SauceSpoon/RBE206TC-submission/ESP32-source/camera璇嗗埆妯″瀷/瑙嗚绯荤粺鏂规.md

颜色分割定位候选区域
CNN 确认形状
摄像头上下扫视扩大视野
连续多帧投票降低误判
机器人慢速接近并持续复核
