SauceSpoon/RBE206TC-submission/ESP32-source/competition plan.pdf

# Competition

RBE206TC

1.5 m

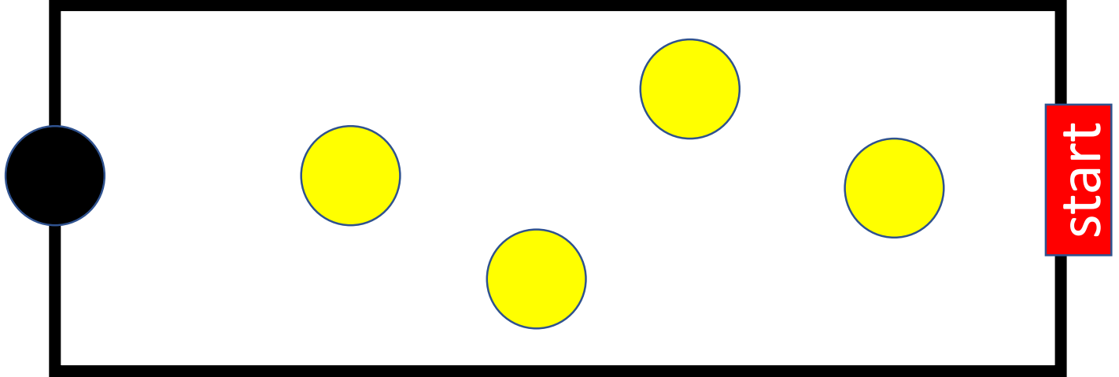
[picture p53: figure]
start

0.6 m

## Task 1

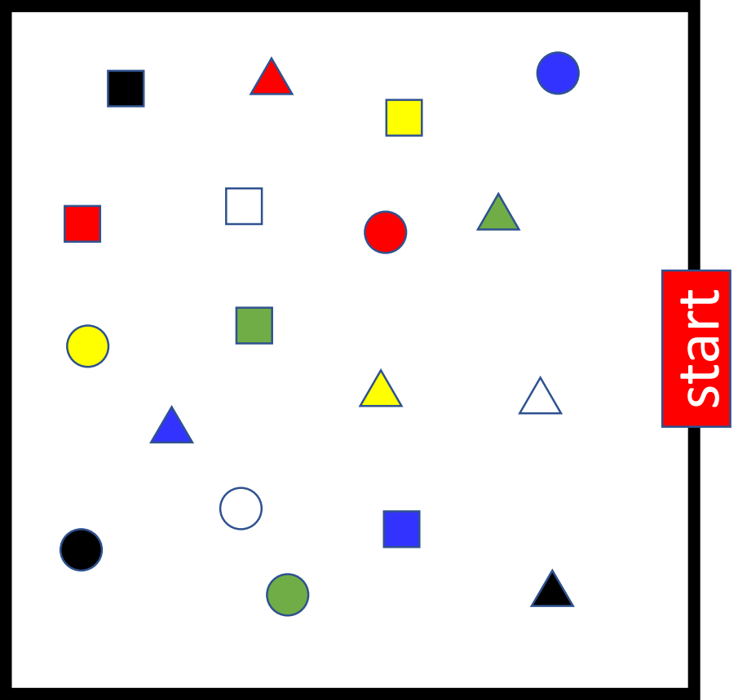
[picture p54: figure]
start

1 m

## Task 2

## Task process

- Phase 1
- Reach the goal
- Touch the black column
- Obstacle avoidance
- 4 obstacles (yellow column)
- Time elapse
- Phase 2
- Select a color and a shape
- Random selection
- Touch the specific object (color and shape)

## - 2 trials - Pick a better performance - Complete a phase before starting the next phase
