SauceSpoon/RBE206TC-submission/oodk(CAD model)/odk4（Generation 4）/cam_mera.SLDASM

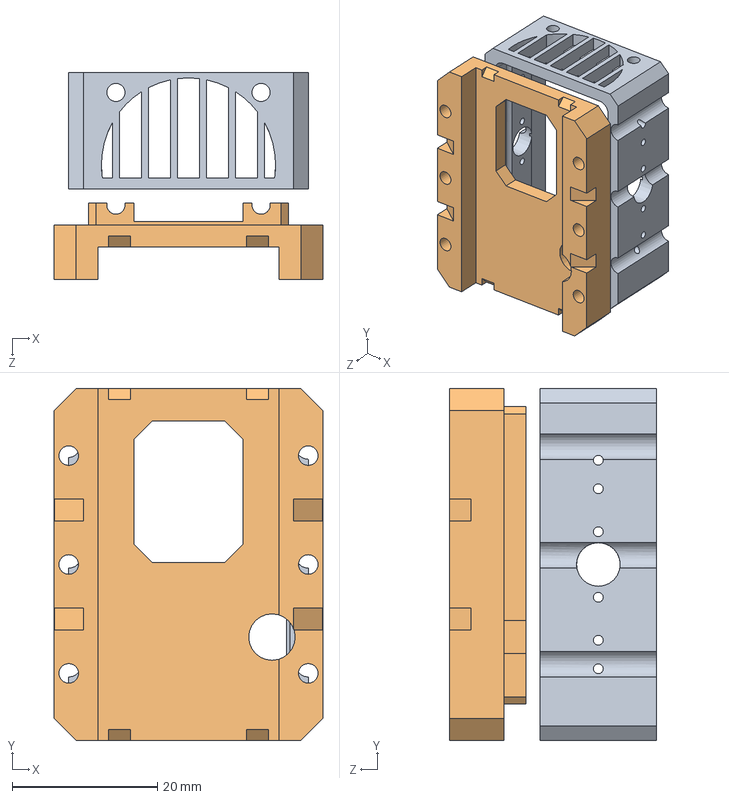
[picture p65: CAD file, 2026-05-20]
oodk(CAD model)/odk4（Generation 4）/cam_mera.SLDASM
37.0 x 48.5 x 28.5 mm
摄像机壳1
摄像机壳2
