SauceSpoon/RBE206TC-submission/oodk(CAD model)/odk2（Generation 2）/odk3.SLDASM

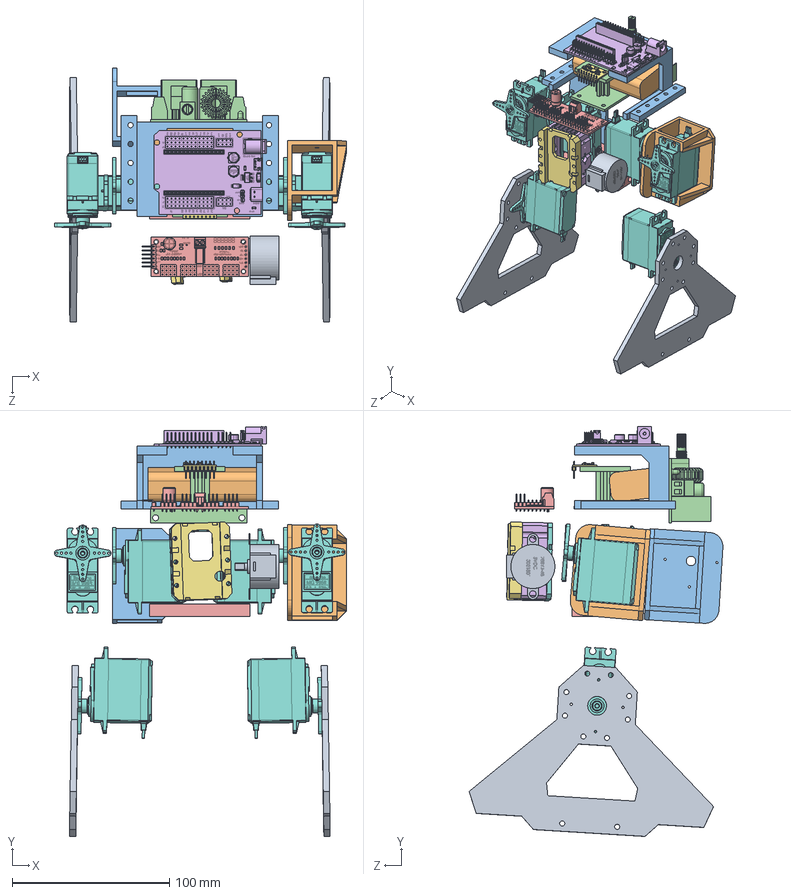
[picture p66: CAD file, 2026-05-20]
oodk(CAD model)/odk2（Generation 2）/odk3.SLDASM
185.7 x 260.6 x 161.3 mm
十字舵机 x 6
MPU6050
ESP32拓展板26
PCA9685
XH-M401 Buck converter (XL4016E1)
esp32_dc
LB218B
Step Motor 28BYJ-48
摄像机壳3
摄像机壳1
摄像机壳2
横_
MPU
髋部连接件-右
髋部连接件-左
