SauceSpoon/RBE206TC-submission/oodk(CAD model)/odk2（Generation 2）/髋.SLDASM

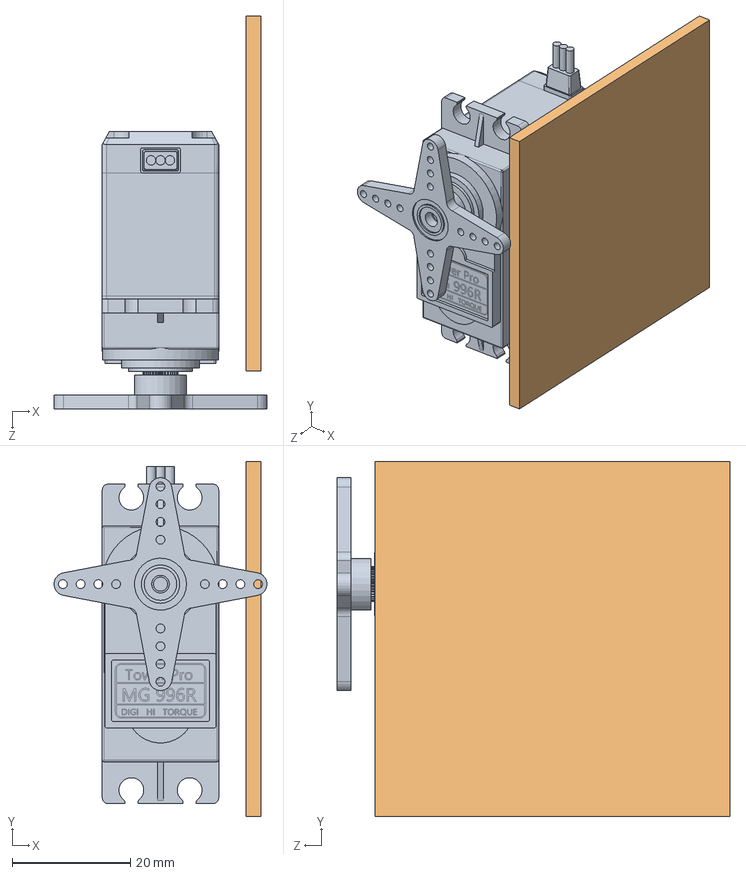
[picture p67: CAD file, 2026-05-20]
oodk(CAD model)/odk2（Generation 2）/髋.SLDASM
36.0 x 60.0 x 66.4 mm
髋连接件
十字舵机
