SauceSpoon/RBE206TC-submission/oodk(CAD model)/odk4（Generation 4）/PCA9685.SLDPRT

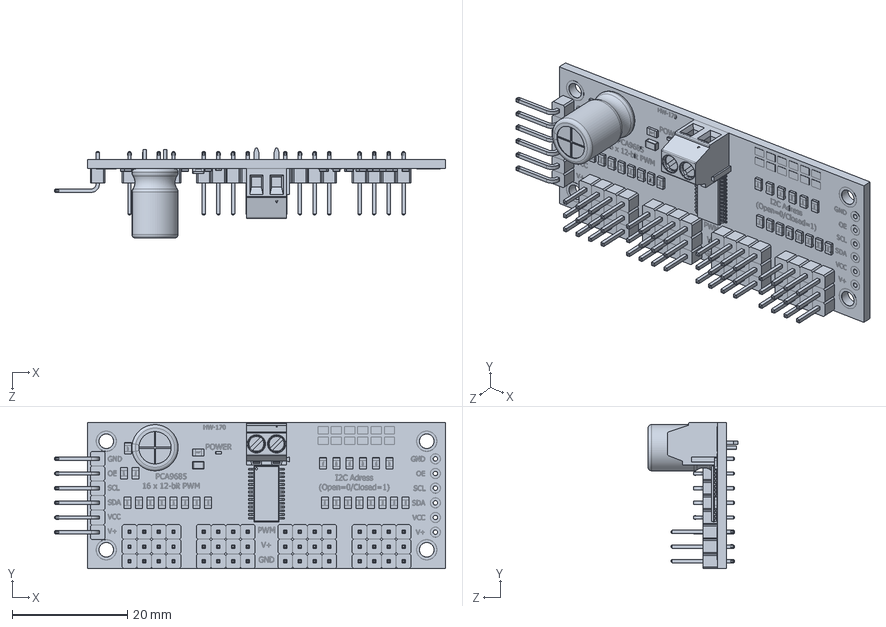
[picture p73: CAD file, 2026-05-20]
oodk(CAD model)/odk4（Generation 4）/PCA9685.SLDPRT
67.7 x 25.3 x 15.6 mm
