SauceSpoon/RBE206TC-submission/oodk(CAD model)/odk4（Generation 4）/print/ESP32-cam.step

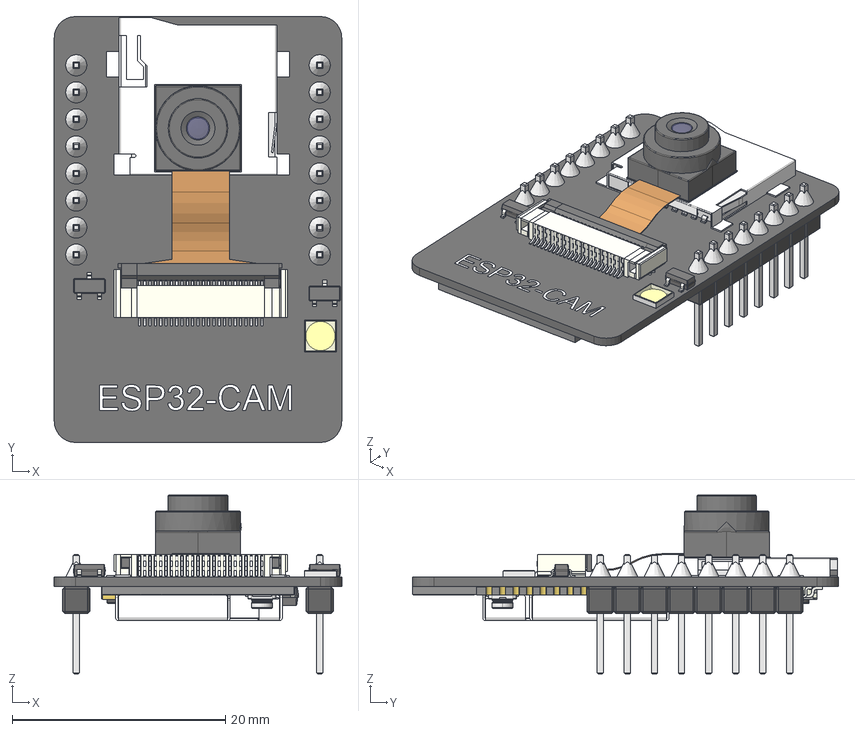
[picture p74: CAD file, 2026-05-20]
oodk(CAD model)/odk4（Generation 4）/print/ESP32-cam.step
27.0 x 40.0 x 16.8 mm
PCB
WiFi antenna
uid__2363^DesignRootModel_PCB_ESP32-S2-SOLO-U_V1_ESP32-S2-SOLO-U_V1
uid__1-263^DesignRootModel_PCB_ESP32-S2-SOLO-U_V1_ESP32-S2-SOLO-U_V1
uid__1-264^DesignRootModel_PCB_ESP32-S2-SOLO-U_V1_ESP32-S2-SOLO-U_V1
20279-001E-01C RECEPTACLE R9 STEP ALL.STEP^20279-001E-01C RECEPTACLE R9 STEP ALL.STEP_Submodel-IPEX_3P_part_DesignRootModel_PCB_ESP32-S2-SOLO-U_V1_ ESP32-S2-SOL
20279-001E-01C RECEPTACLE R9 STEP ALL.STEP^20279-001E-01C RECEPTACLE R9 STEP ALL.STEP_Submodel-IPEX_3P_part_DesignRootModel_PCB_ESP32-S2-SOLO-U_V1_ ESP32-S2-SOL
ESP32-WROOM-32U_Shieldingcase_20210312
SOIC_8_1EP_39x49mm_P127mm
SW_SPST_B3U-1000P
SOT_223
CP_EIA_3528_12_Kemet_T
FPC-24
FPC-025
FPC-026
FPC-027
FPC-028
FPC-029
FPC-030
FPC-031
FPC-032
FPC-033
FPC-034
FPC-035
FPC-036
FPC-037
FPC-038
FPC-039
FPC-040
scotxh
SOT_23-1
SOT_23-2
Text
