SauceSpoon/RBE206TC-submission/oodk(CAD model)/odk2（Generation 2）/28BYJ-48步进电机和ULN2003步进电机驱动板/28BYJ-48_5VDC.step

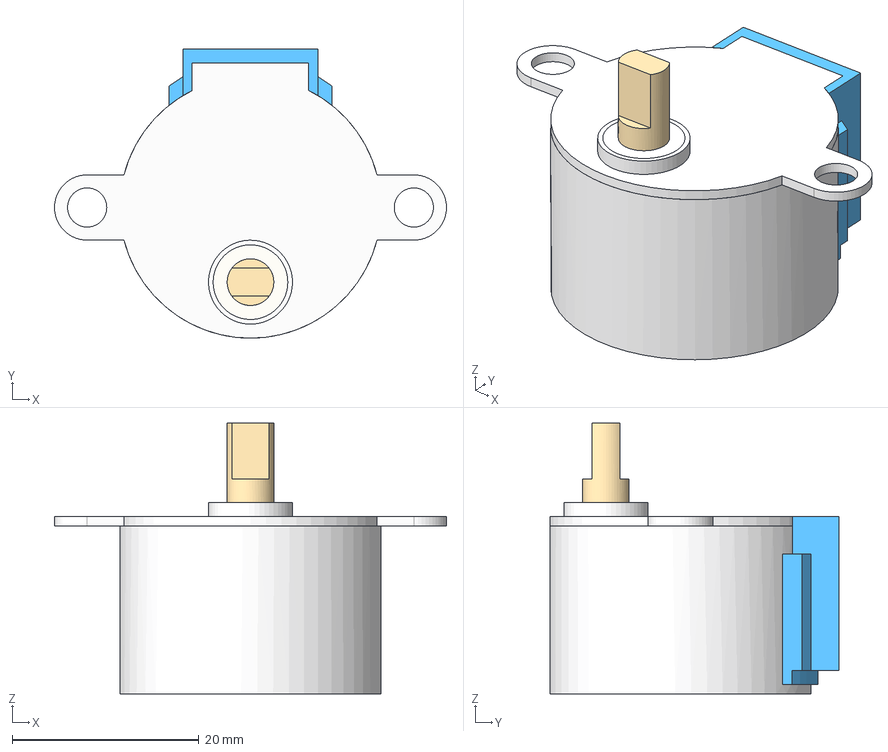
[picture p76: CAD file, 2026-05-20]
oodk(CAD model)/odk2（Generation 2）/28BYJ-48步进电机和ULN2003步进电机驱动板/28BYJ-48_5VDC.step
42.0 x 31.0 x 29.0 mm
