SauceSpoon/RBE206TC-submission/oodk(CAD model)/odk2（Generation 2）/髋连接件.SLDPRT

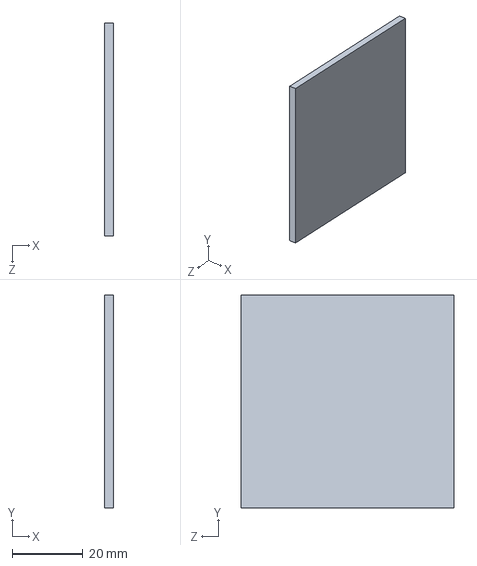
[picture p77: CAD file, 2026-05-20]
oodk(CAD model)/odk2（Generation 2）/髋连接件.SLDPRT
2.50 x 60.0 x 60.0 mm
