SauceSpoon/RBE206TC-submission/oodk(CAD model)/odk3（Generation 3）/print/22.STEP

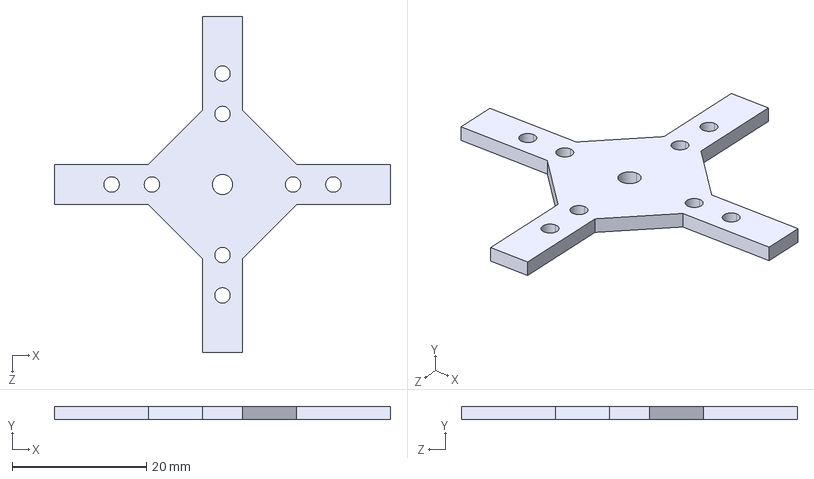
[picture p78: CAD file, 2026-05-20]
oodk(CAD model)/odk3（Generation 3）/print/22.STEP
50.0 x 2.00 x 50.0 mm
