SauceSpoon/RBE206TC-submission/oodk(CAD model)/odk3（Generation 3）/横_.SLDPRT

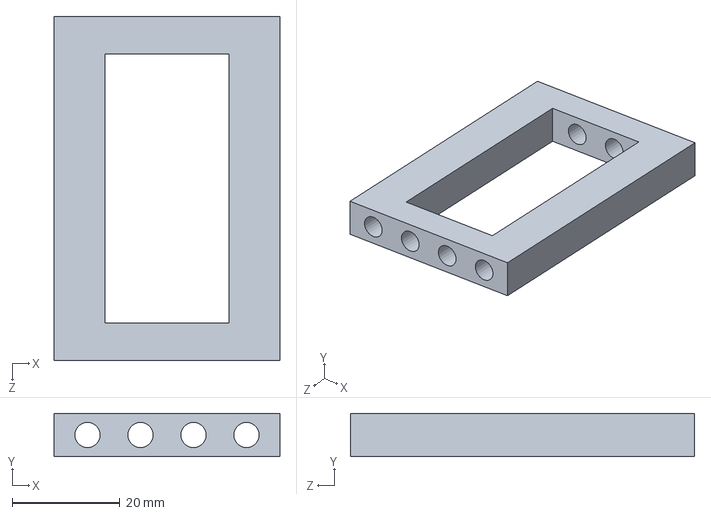
[picture p79: CAD file, 2026-05-20]
oodk(CAD model)/odk3（Generation 3）/横_.SLDPRT
42.0 x 8.00 x 64.0 mm
