SauceSpoon/RBE206TC-submission/oodk(CAD model)/odk4（Generation 4）/camera_g.SLDPRT

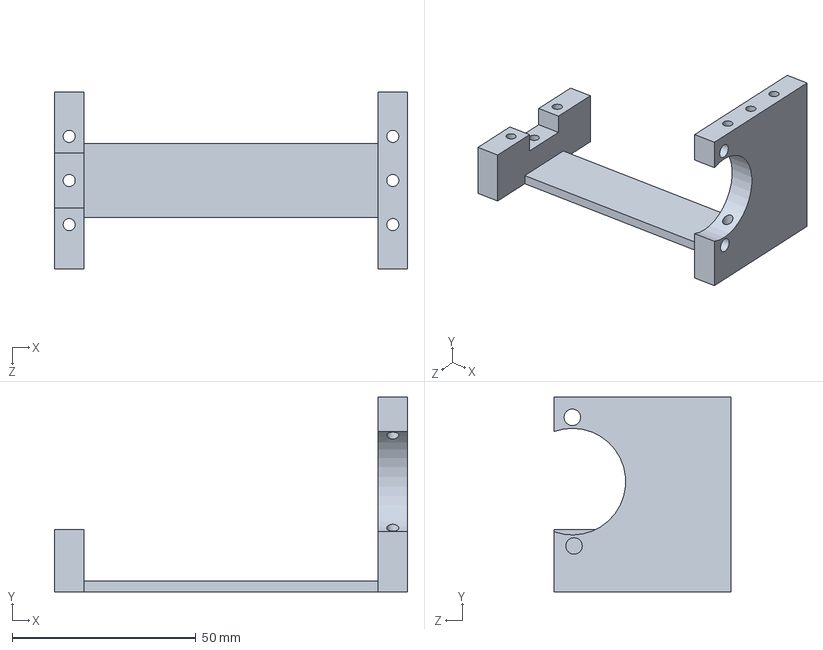
[picture p80: CAD file, 2026-05-20]
oodk(CAD model)/odk4（Generation 4）/camera_g.SLDPRT
96.0 x 53.0 x 48.1 mm
