SauceSpoon/RBE206TC-submission/oodk(CAD model)/odk4（Generation 4）/print/新plat.STEP

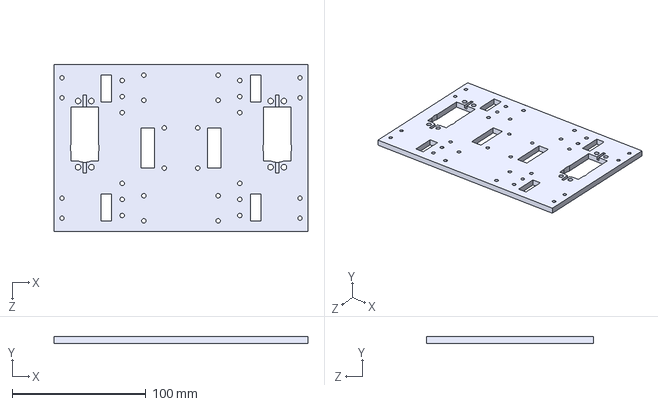
[picture p81: CAD file, 2026-05-20]
oodk(CAD model)/odk4（Generation 4）/print/新plat.STEP
190.0 x 5.00 x 125.0 mm
