SauceSpoon/RBE206TC-submission/oodk(CAD model)/odk1（Generation 1）/髋部连接件-左.SLDPRT

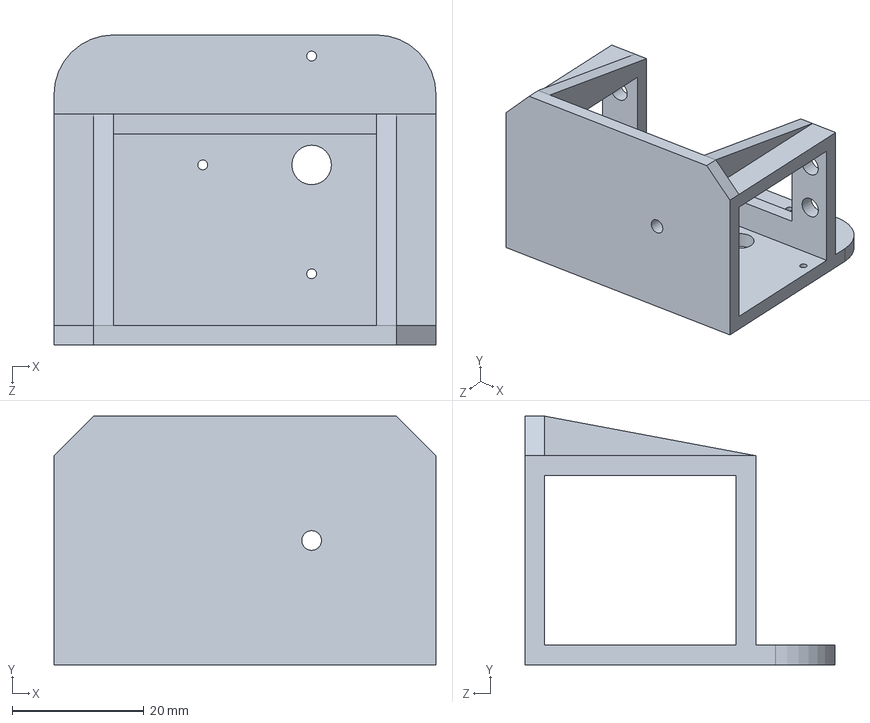
[picture p82: CAD file, 2026-05-20]
oodk(CAD model)/odk1（Generation 1）/髋部连接件-左.SLDPRT
57.9 x 37.7 x 47.0 mm
