SauceSpoon/RBE206TC-submission/oodk(CAD model)/odk2（Generation 2）/332.SLDPRT

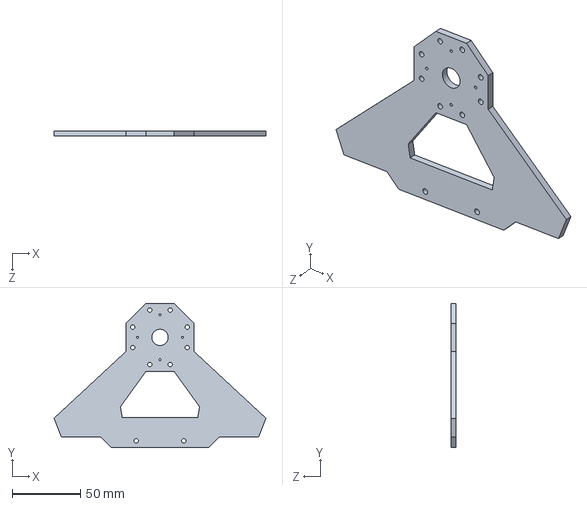
[picture p83: CAD file, 2026-05-20]
oodk(CAD model)/odk2（Generation 2）/332.SLDPRT
155.7 x 106.0 x 4.00 mm
