SauceSpoon/RBE206TC-submission/oodk(CAD model)/odk3（Generation 3）/print/板1.STEP

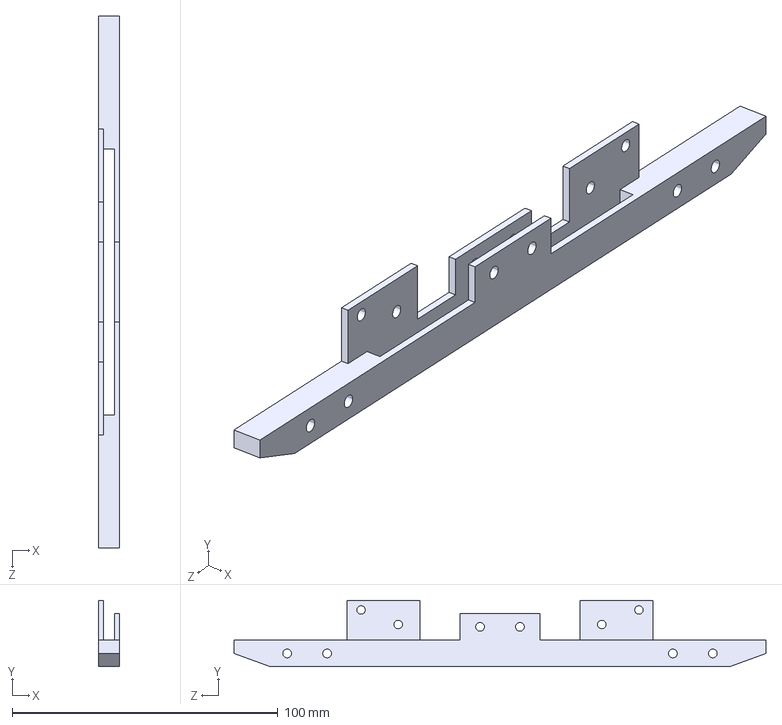
[picture p84: CAD file, 2026-05-20]
oodk(CAD model)/odk3（Generation 3）/print/板1.STEP
8.00 x 25.0 x 200.0 mm
