SauceSpoon/RBE206TC-submission/oodk(CAD model)/odk3（Generation 3）/摄像机壳1.SLDPRT

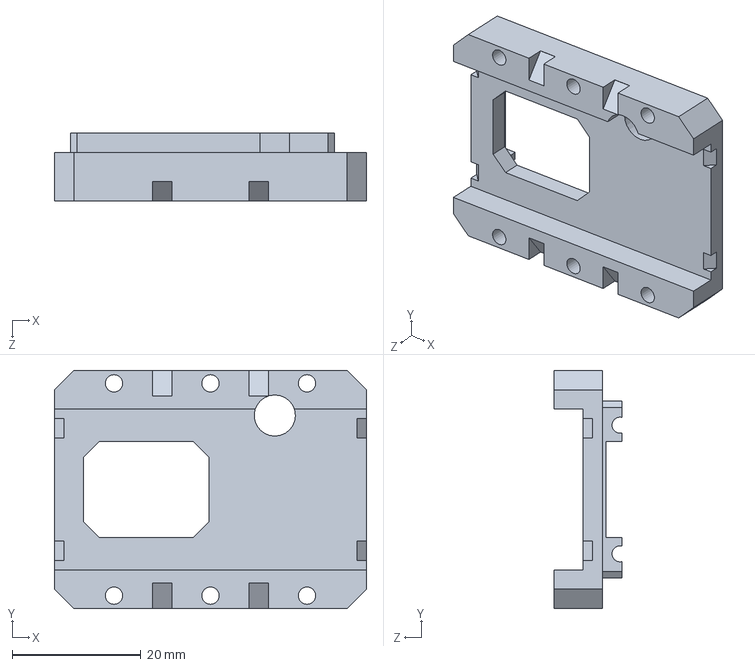
[picture p85: CAD file, 2026-05-20]
oodk(CAD model)/odk3（Generation 3）/摄像机壳1.SLDPRT
48.5 x 37.0 x 10.5 mm
