SauceSpoon/RBE206TC-submission/oodk(CAD model)/odk4（Generation 4）/MPU6050.SLDPRT

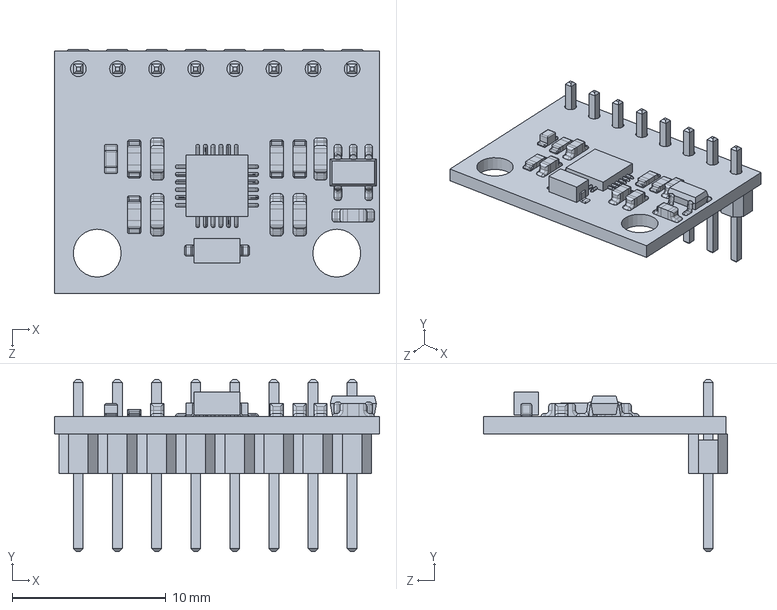
[picture p86: CAD file, 2026-05-20]
oodk(CAD model)/odk4（Generation 4）/MPU6050.SLDPRT
21.1 x 11.2 x 15.9 mm
