SauceSpoon/RBE206TC-submission/oodk(CAD model)/odk1（Generation 1）/小腿.SLDPRT

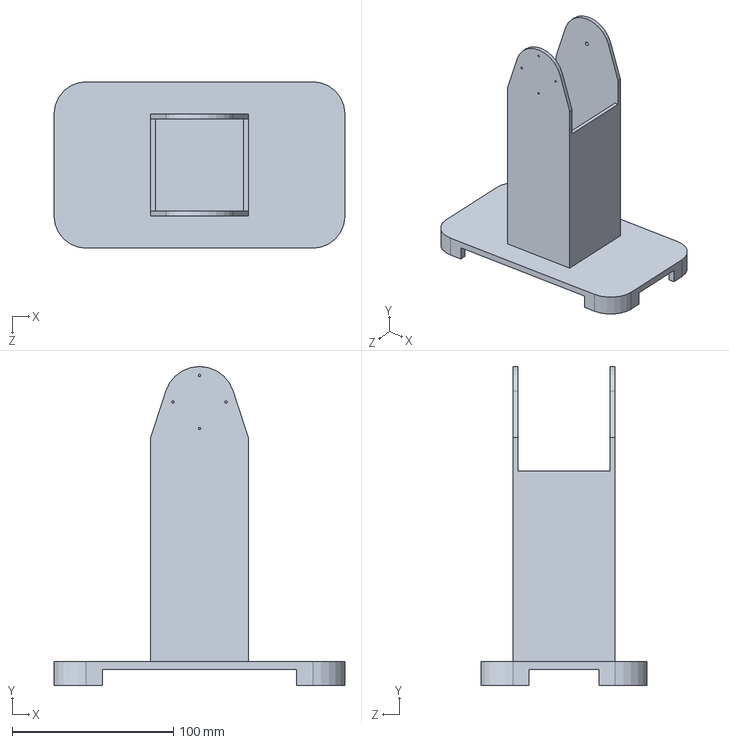
[picture p87: CAD file, 2026-05-20]
oodk(CAD model)/odk1（Generation 1）/小腿.SLDPRT
180.6 x 198.0 x 103.3 mm
