SauceSpoon/RBE206TC-submission/oodk(CAD model)/odk2（Generation 2）/print/架.STEP

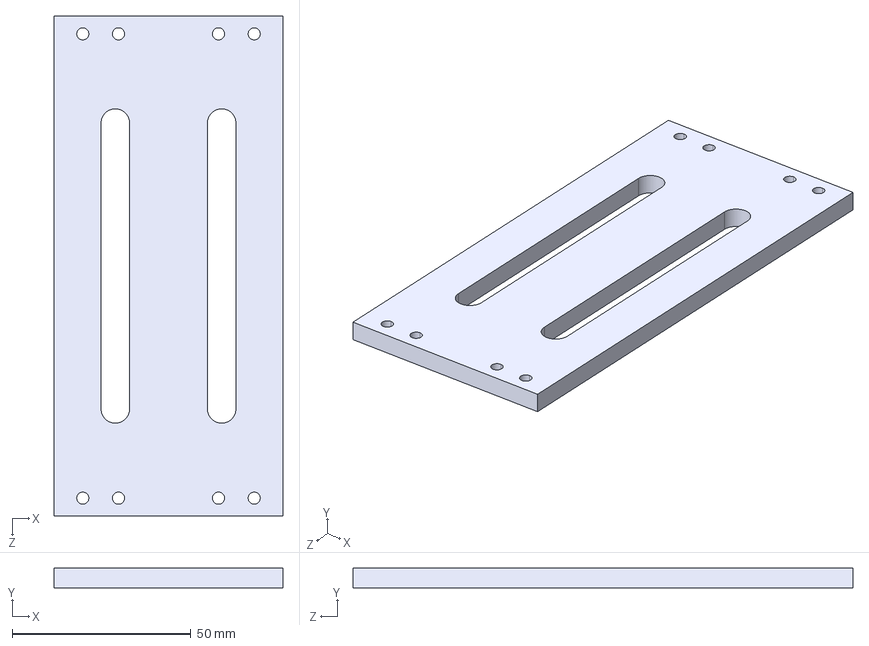
[picture p88: CAD file, 2026-05-20]
oodk(CAD model)/odk2（Generation 2）/print/架.STEP
64.0 x 5.50 x 140.0 mm
