SauceSpoon/RBE206TC-submission/oodk(CAD model)/odk4（Generation 4）/MPU.SLDPRT

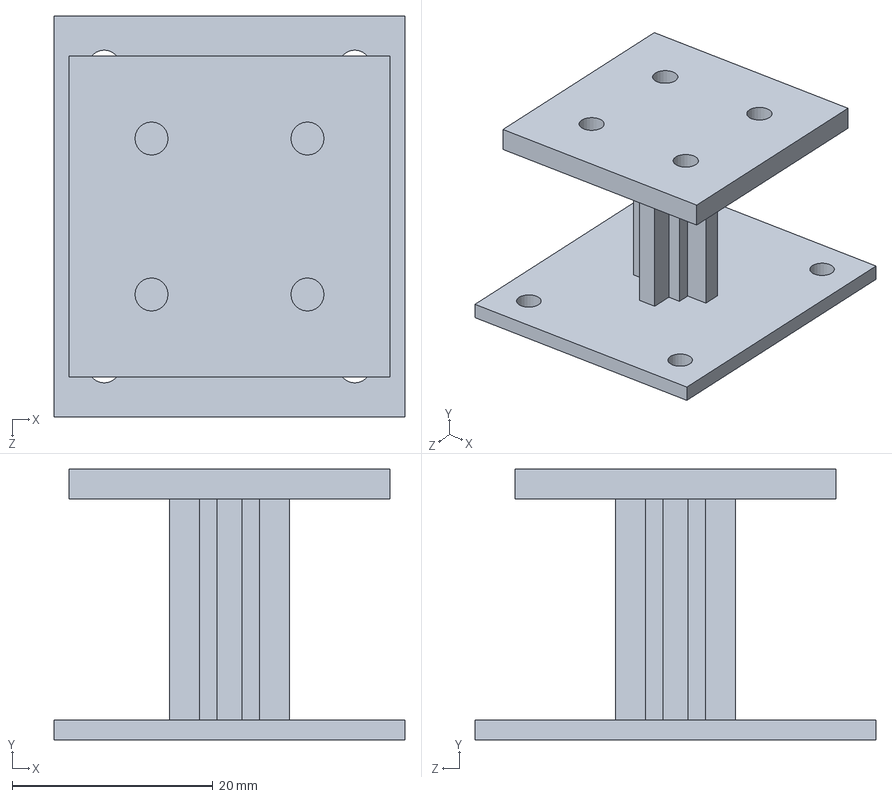
[picture p89: CAD file, 2026-05-20]
oodk(CAD model)/odk4（Generation 4）/MPU.SLDPRT
35.0 x 27.0 x 40.0 mm
