SauceSpoon/RBE206TC-submission/oodk(CAD model)/odk2（Generation 2）/print/Mirrorthigh2.3mf

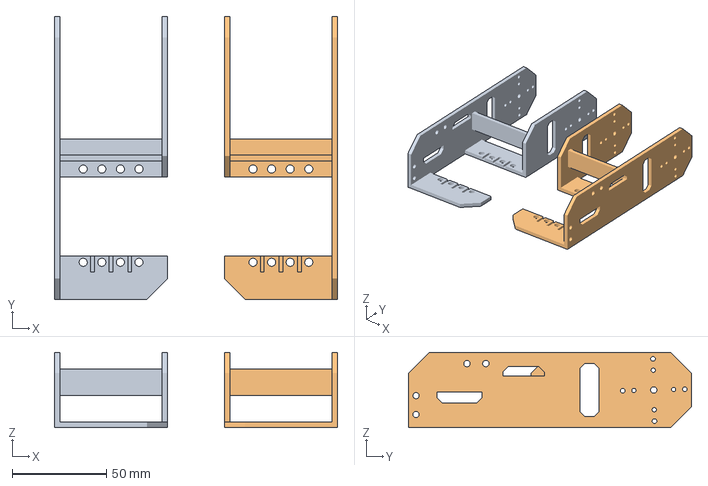
[picture p91: CAD file, 2026-05-20]
oodk(CAD model)/odk2（Generation 2）/print/Mirrorthigh2.3mf
150.0 x 150.0 x 40.0 mm
thigh.STEP
Mirrorthigh.STEP
