SauceSpoon/RBE206TC-submission/oodk(CAD model)/odk2（Generation 2）/XH-M401 Buck converter (XL4016E1).SLDPRT

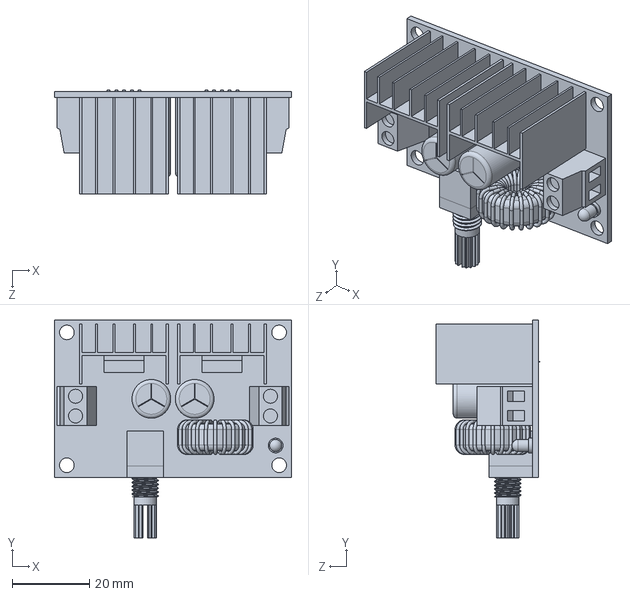
[picture p92: CAD file, 2026-05-20]
oodk(CAD model)/odk2（Generation 2）/XH-M401 Buck converter (XL4016E1).SLDPRT
61.3 x 56.4 x 27.0 mm
