SauceSpoon/RBE206TC-submission/oodk(CAD model)/odk1（Generation 1）/髋部.SLDPRT

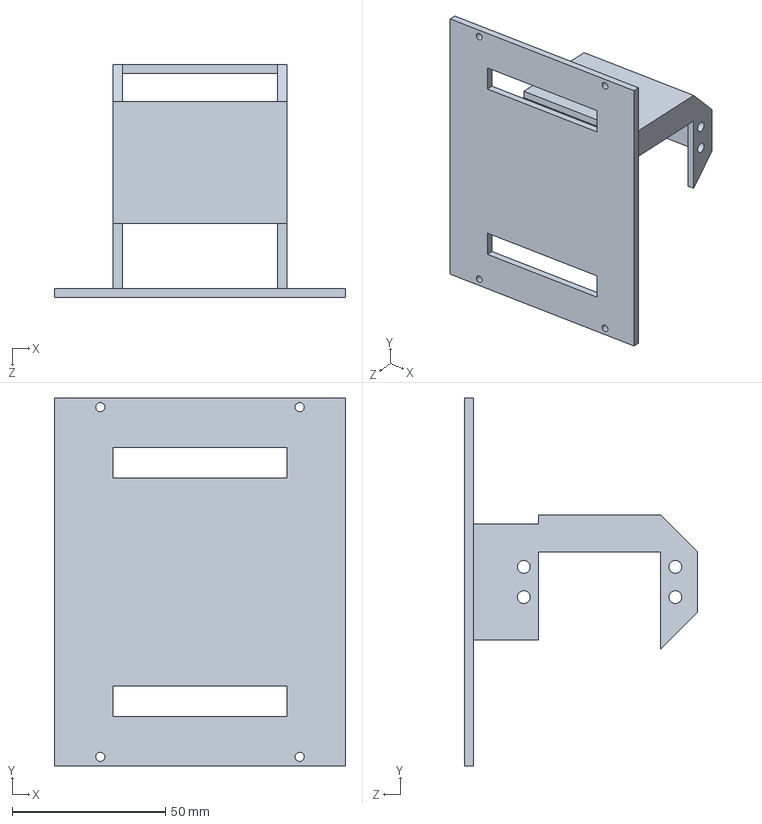
[picture p93: CAD file, 2026-05-20]
oodk(CAD model)/odk1（Generation 1）/髋部.SLDPRT
95.0 x 120.0 x 76.0 mm
