SauceSpoon/RBE206TC-submission/oodk(CAD model)/odk2（Generation 2）/大腿.SLDPRT

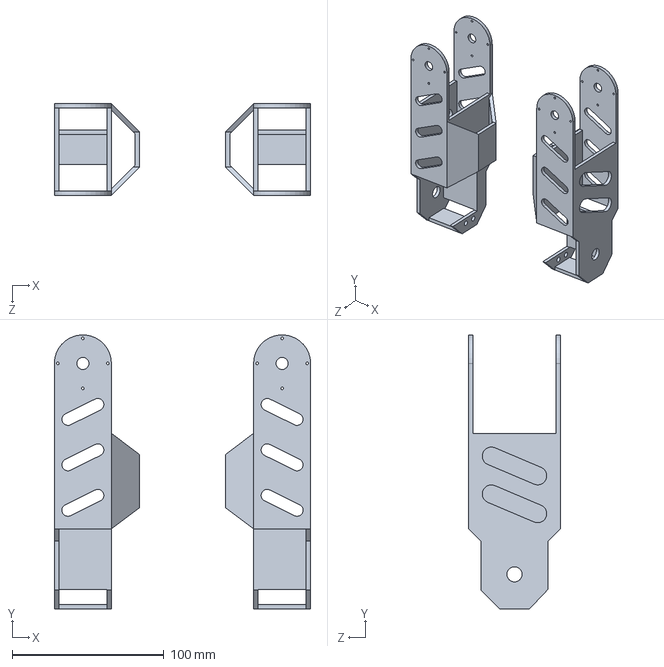
[picture p94: CAD file, 2026-05-20]
oodk(CAD model)/odk2（Generation 2）/大腿.SLDPRT
169.2 x 180.8 x 60.6 mm
