SauceSpoon/RBE206TC-submission/oodk(CAD model)/odk3（Generation 3）/print/HC_loa.STEP

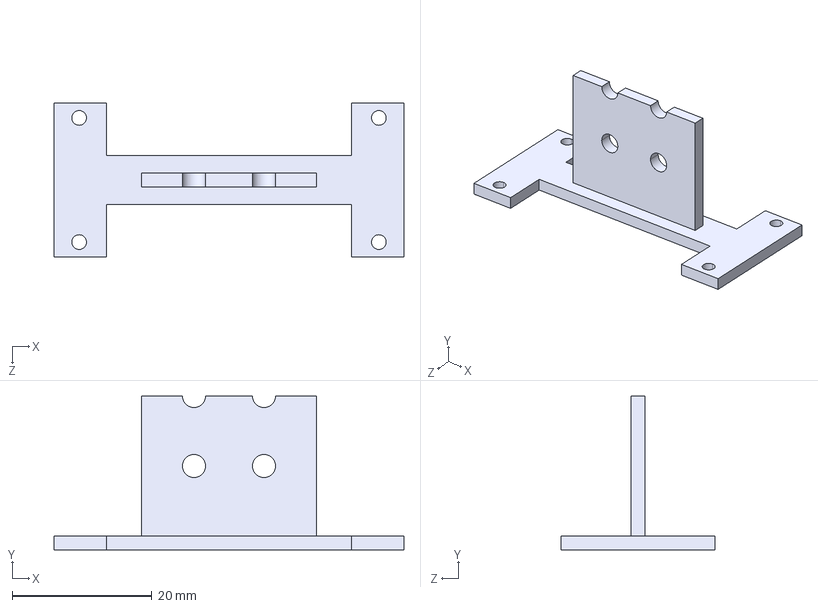
[picture p95: CAD file, 2026-05-20]
oodk(CAD model)/odk3（Generation 3）/print/HC_loa.STEP
50.0 x 22.0 x 22.0 mm
