SauceSpoon/RBE206TC-submission/oodk(CAD model)/odk4（Generation 4）/print/2_f_.3mf

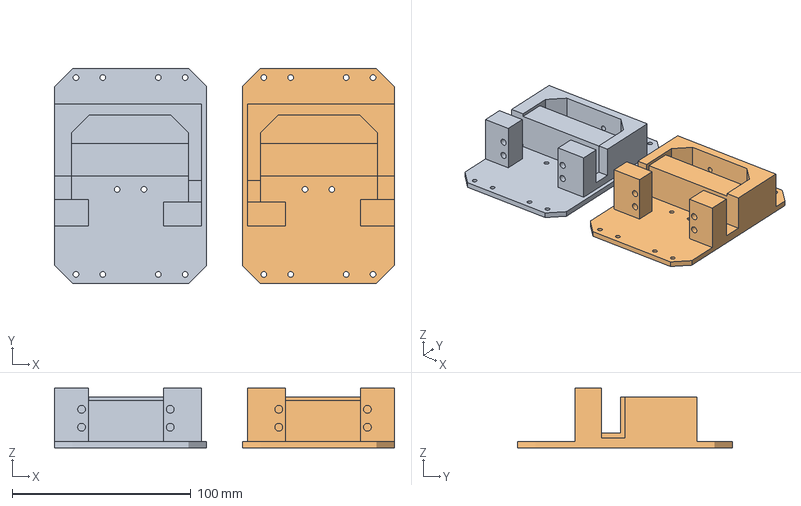
[picture p96: CAD file, 2026-05-20]
oodk(CAD model)/odk4（Generation 4）/print/2_f_.3mf
190.0 x 120.0 x 33.5 mm
feet1.STEP
Mirrorfeet1.STEP
