SauceSpoon/RBE206TC-submission/oodk(CAD model)/odk3（Generation 3）/print/thigh.STEP

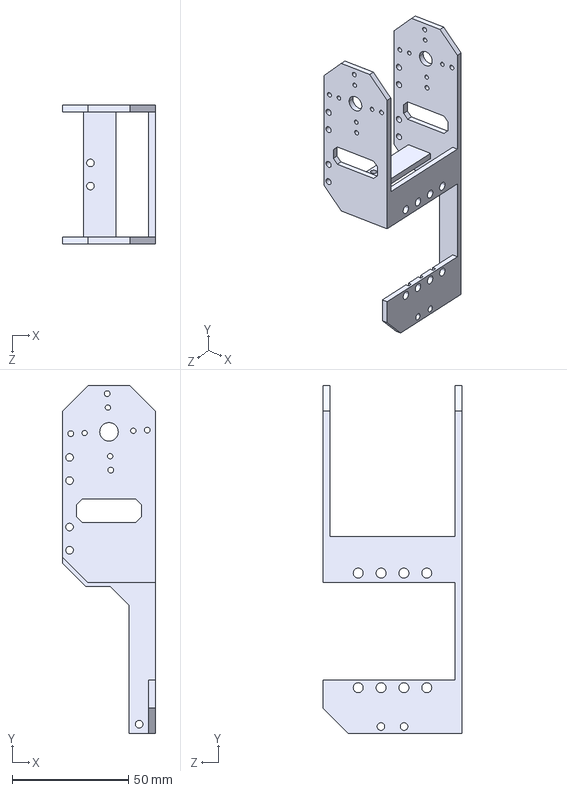
[picture p97: CAD file, 2026-05-20]
oodk(CAD model)/odk3（Generation 3）/print/thigh.STEP
40.0 x 150.0 x 60.0 mm
