SauceSpoon/RBE206TC-submission/oodk(CAD model)/odk3（Generation 3）/髋部连接件.SLDPRT

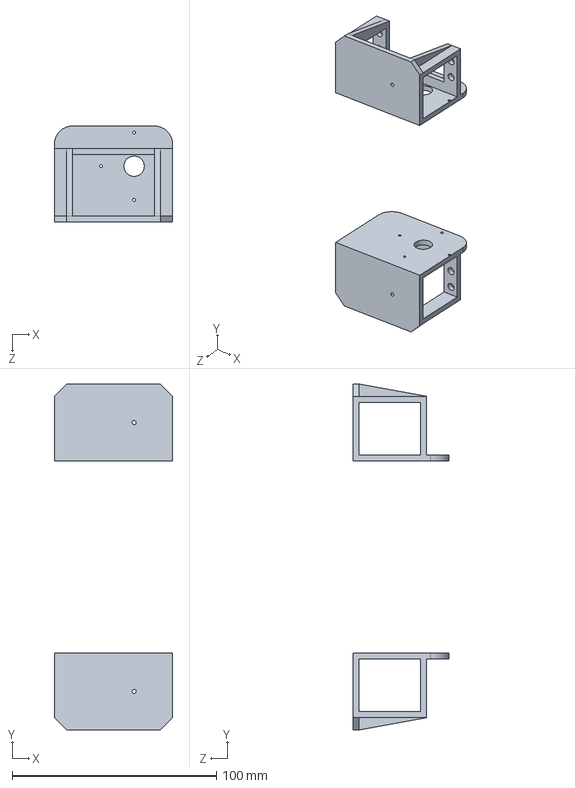
[picture p98: CAD file, 2026-05-20]
oodk(CAD model)/odk3（Generation 3）/髋部连接件.SLDPRT
57.9 x 169.2 x 47.0 mm
