SauceSpoon/RBE206TC-submission/oodk(CAD model)/odk4（Generation 4）/ESP32拓展板26.SLDPRT

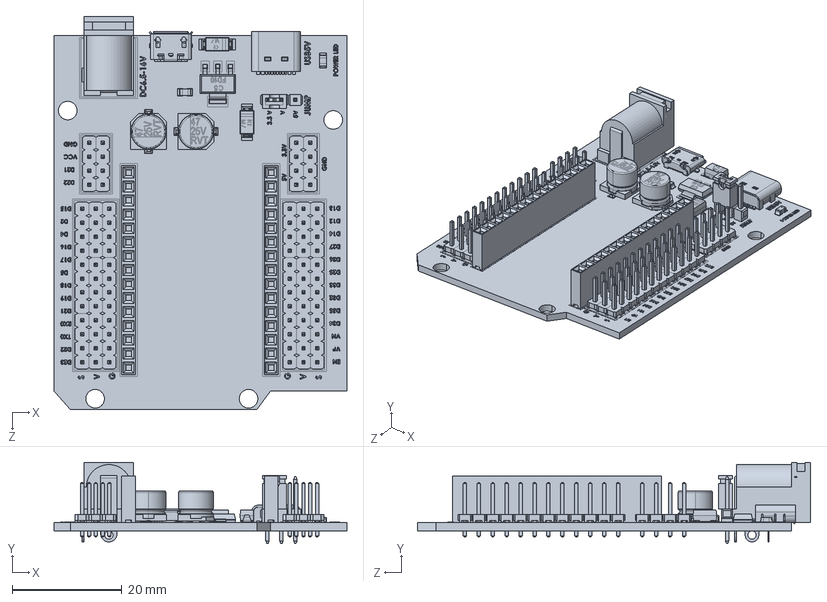
[picture p99: CAD file, 2026-05-20]
oodk(CAD model)/odk4（Generation 4）/ESP32拓展板26.SLDPRT
53.4 x 14.8 x 71.7 mm
