SauceSpoon/RBE206TC-submission/oodk(CAD model)/odk4（Generation 4）/print/摄像机壳1.STEP

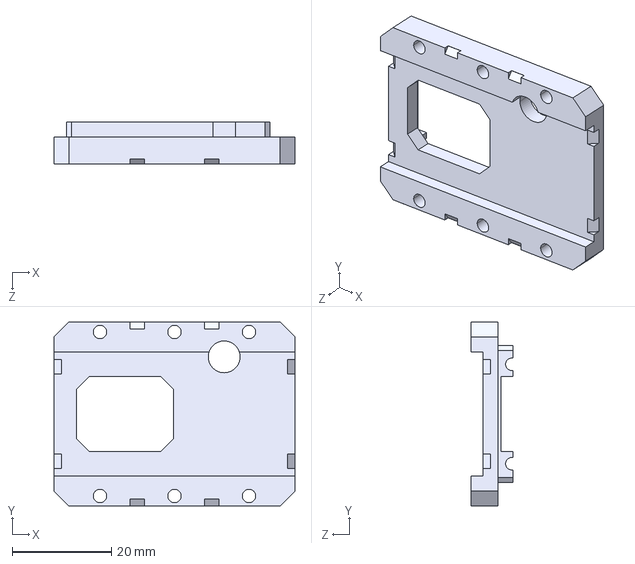
[picture p100: CAD file, 2026-05-20]
oodk(CAD model)/odk4（Generation 4）/print/摄像机壳1.STEP
48.5 x 37.0 x 8.53 mm
