SauceSpoon/RBE206TC-submission/oodk(CAD model)/odk2（Generation 2）/print/esp32_dc.STEP

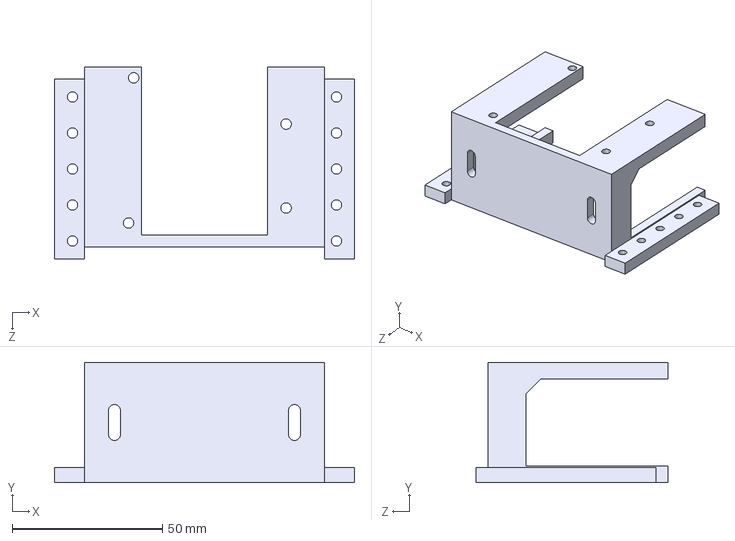
[picture p101: CAD file, 2026-05-20]
oodk(CAD model)/odk2（Generation 2）/print/esp32_dc.STEP
100.0 x 40.0 x 64.0 mm
