SauceSpoon/RBE206TC-submission/oodk(CAD model)/odk3（Generation 3）/print/HC_loa_th.3mf

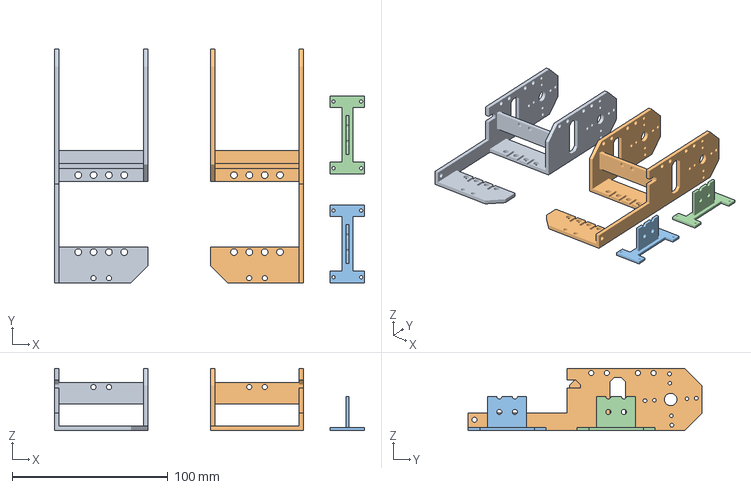
[picture p102: CAD file, 2026-05-20]
oodk(CAD model)/odk3（Generation 3）/print/HC_loa_th.3mf
199.0 x 150.0 x 40.0 mm
thigh2.STEP x 2
HC_loa.STEP x 2
