SauceSpoon/RBE206TC-submission/oodk(CAD model)/odk4（Generation 4）/LB218B.SLDPRT

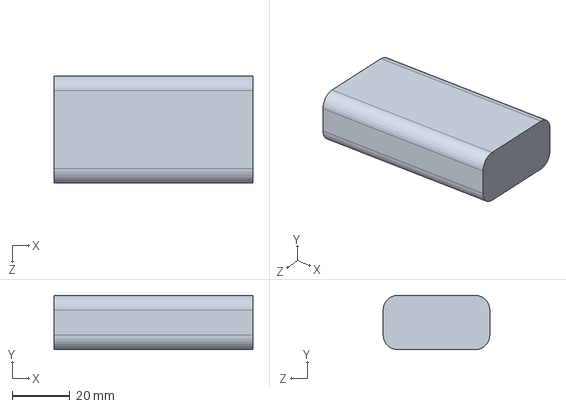
[picture p103: CAD file, 2026-05-20]
oodk(CAD model)/odk4（Generation 4）/LB218B.SLDPRT
69.0 x 18.8 x 37.0 mm
