SauceSpoon/RBE206TC-submission/oodk(CAD model)/odk4（Generation 4）/print/59.3mf

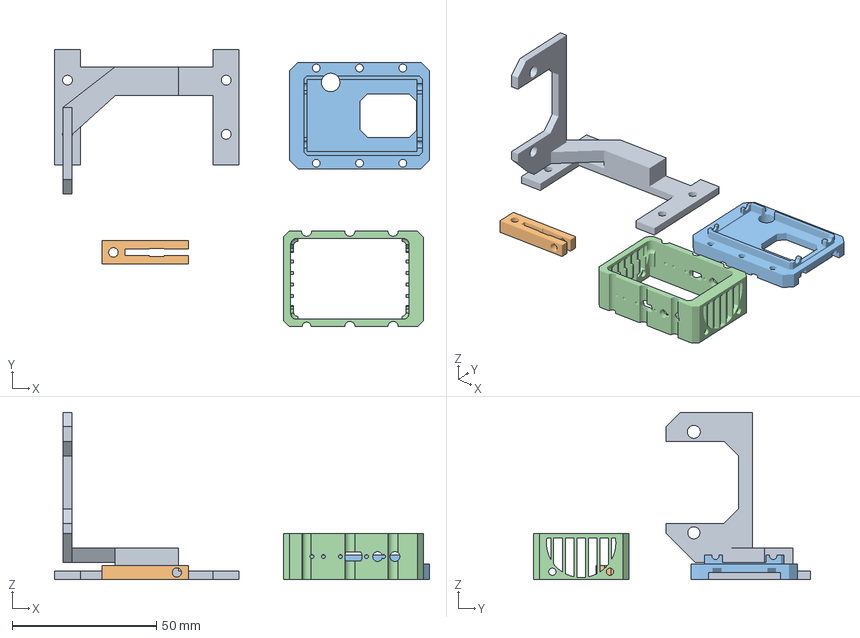
[picture p104: CAD file, 2026-05-20]
oodk(CAD model)/odk4（Generation 4）/print/59.3mf
130.0 x 96.0 x 58.0 mm
cccc.STEP
夹.STEP
摄像机壳1.STEP
摄像机壳2.STEP
