SauceSpoon/RBE206TC-submission/oodk(CAD model)/odk4（Generation 4）/Servo disc.SLDPRT

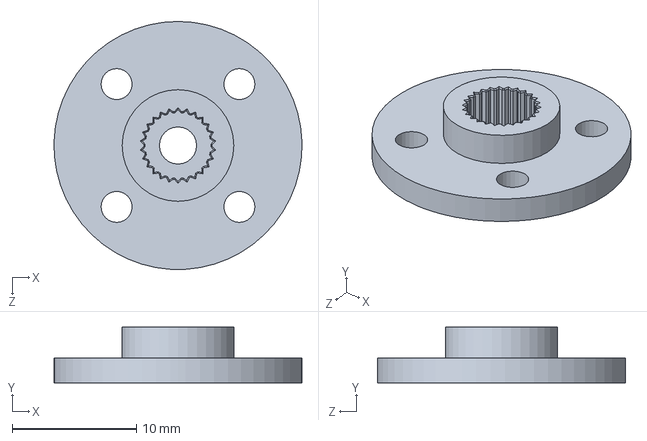
[picture p105: CAD file, 2026-05-20]
oodk(CAD model)/odk4（Generation 4）/Servo disc.SLDPRT
20.0 x 4.50 x 20.0 mm
