SauceSpoon/RBE206TC-submission/oodk(CAD model)/odk2（Generation 2）/摄像机壳3.SLDPRT

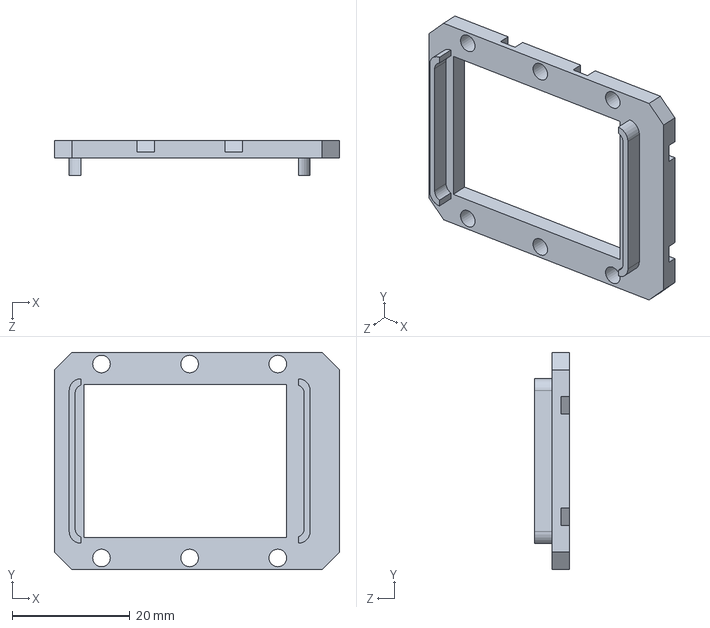
[picture p106: CAD file, 2026-05-20]
oodk(CAD model)/odk2（Generation 2）/摄像机壳3.SLDPRT
48.5 x 37.0 x 6.03 mm
