SauceSpoon/RBE206TC-submission/oodk(CAD model)/odk3（Generation 3）/摄像机壳2.SLDPRT

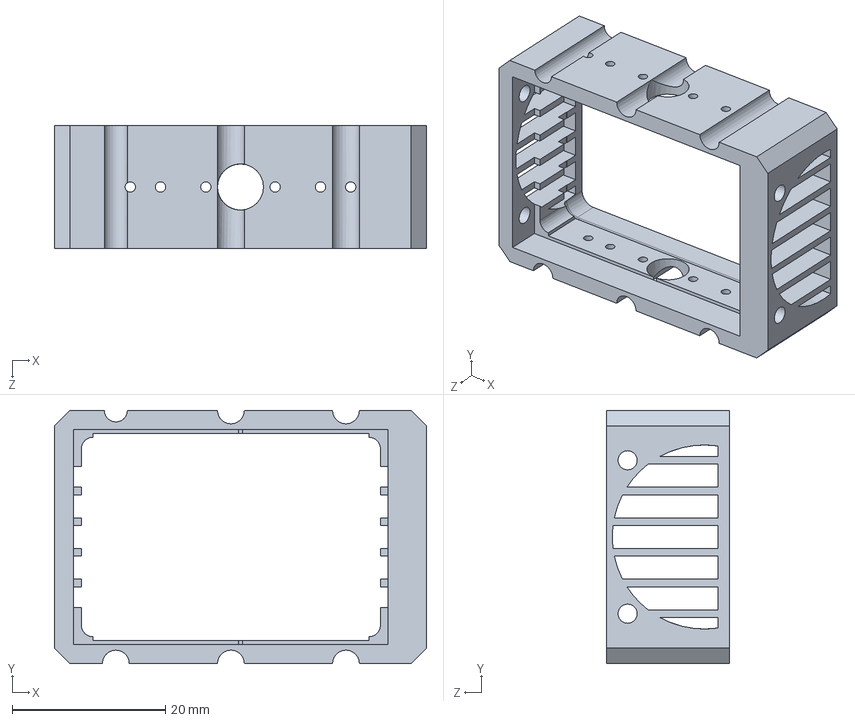
[picture p107: CAD file, 2026-05-20]
oodk(CAD model)/odk3（Generation 3）/摄像机壳2.SLDPRT
48.5 x 33.0 x 16.0 mm
