SauceSpoon/RBE206TC-submission/oodk(CAD model)/odk2（Generation 2）/横2_.SLDPRT

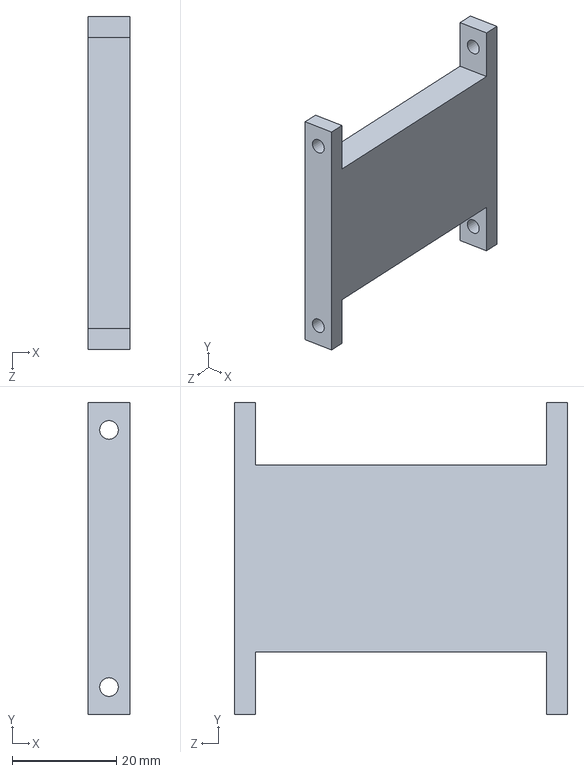
[picture p108: CAD file, 2026-05-20]
oodk(CAD model)/odk2（Generation 2）/横2_.SLDPRT
8.00 x 60.0 x 64.0 mm
