SauceSpoon/RBE206TC-submission/oodk(CAD model)/odk3（Generation 3）/print/4_11.3mf

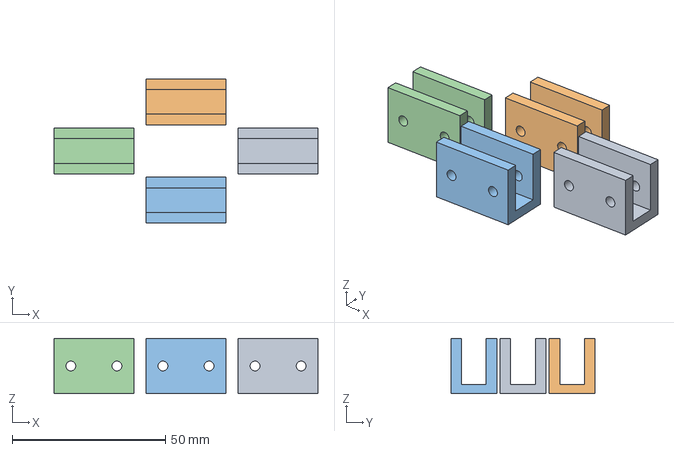
[picture p109: CAD file, 2026-05-20]
oodk(CAD model)/odk3（Generation 3）/print/4_11.3mf
86.0 x 47.0 x 18.0 mm
11.STEP x 4
