SauceSpoon/RBE206TC-submission/oodk(CAD model)/odk4（Generation 4）/print/cd2.STEP

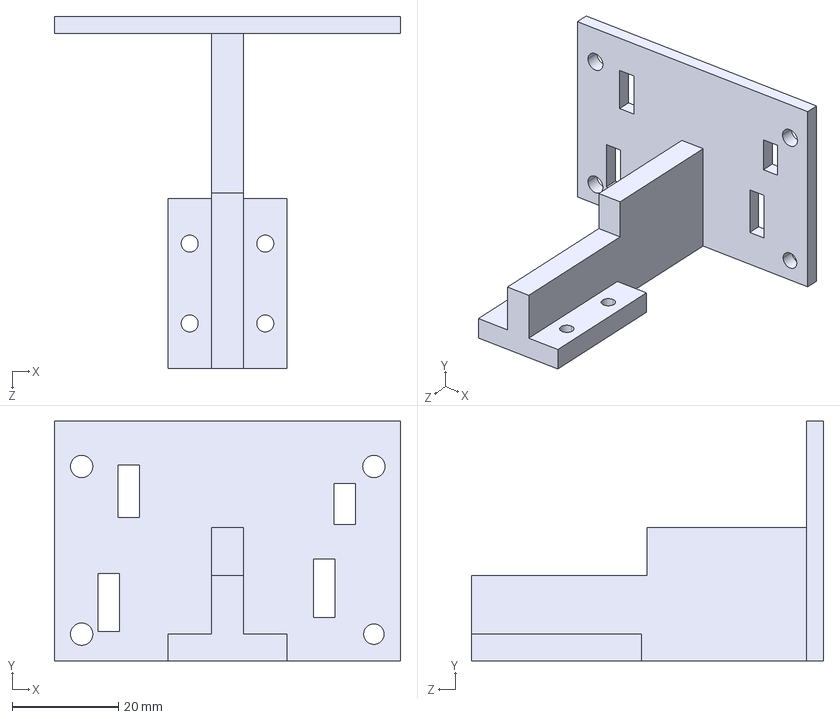
[picture p110: CAD file, 2026-05-20]
oodk(CAD model)/odk4（Generation 4）/print/cd2.STEP
65.0 x 45.0 x 66.2 mm
