SauceSpoon/RBE206TC-submission/oodk(CAD model)/odk2（Generation 2）/print/3.3mf

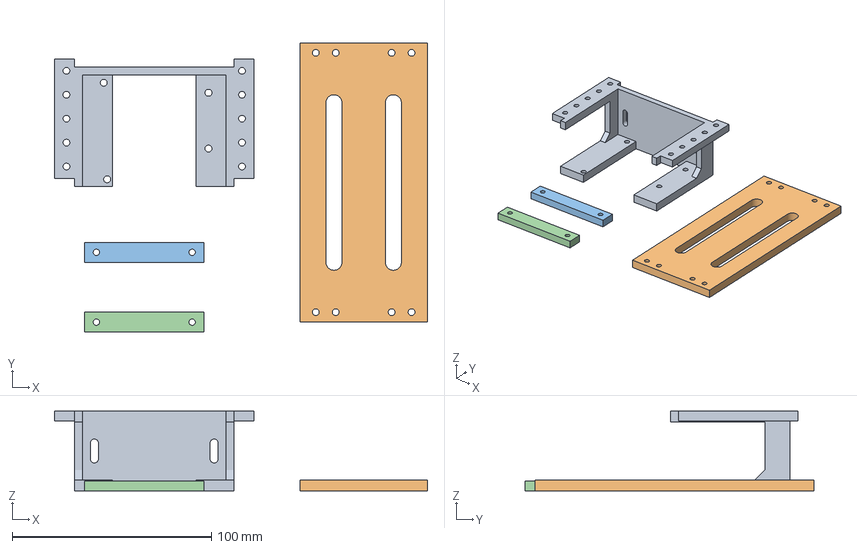
[picture p111: CAD file, 2026-05-20]
oodk(CAD model)/odk2（Generation 2）/print/3.3mf
187.0 x 145.0 x 40.0 mm
esp32_dc.STEP
架.STEP
22.STEP x 2
