SauceSpoon/RBE206TC-submission/oodk(CAD model)/odk4（Generation 4）/Mirrorcd.SLDPRT

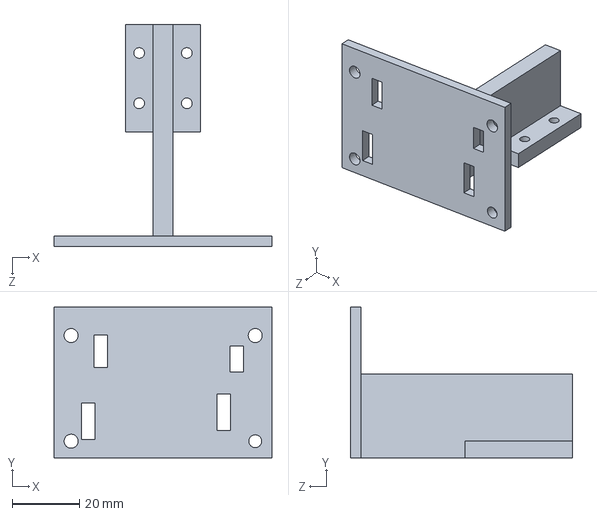
[picture p112: CAD file, 2026-05-20]
oodk(CAD model)/odk4（Generation 4）/Mirrorcd.SLDPRT
65.0 x 45.0 x 66.2 mm
