SauceSpoon/RBE206TC-submission/oodk(CAD model)/odk4（Generation 4）/print/34.STEP

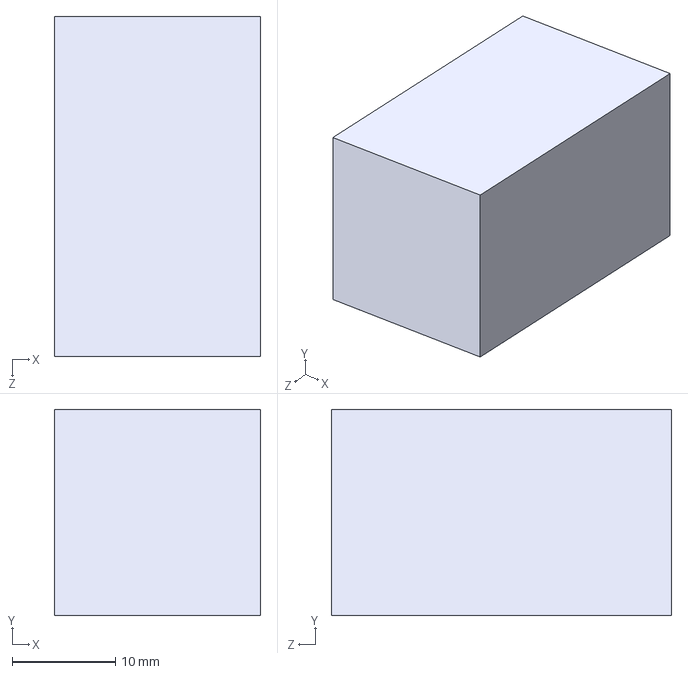
[picture p113: CAD file, 2026-05-20]
oodk(CAD model)/odk4（Generation 4）/print/34.STEP
20.0 x 20.0 x 33.0 mm
