SauceSpoon/RBE206TC-submission/oodk(CAD model)/odk4（Generation 4）/444.SLDPRT

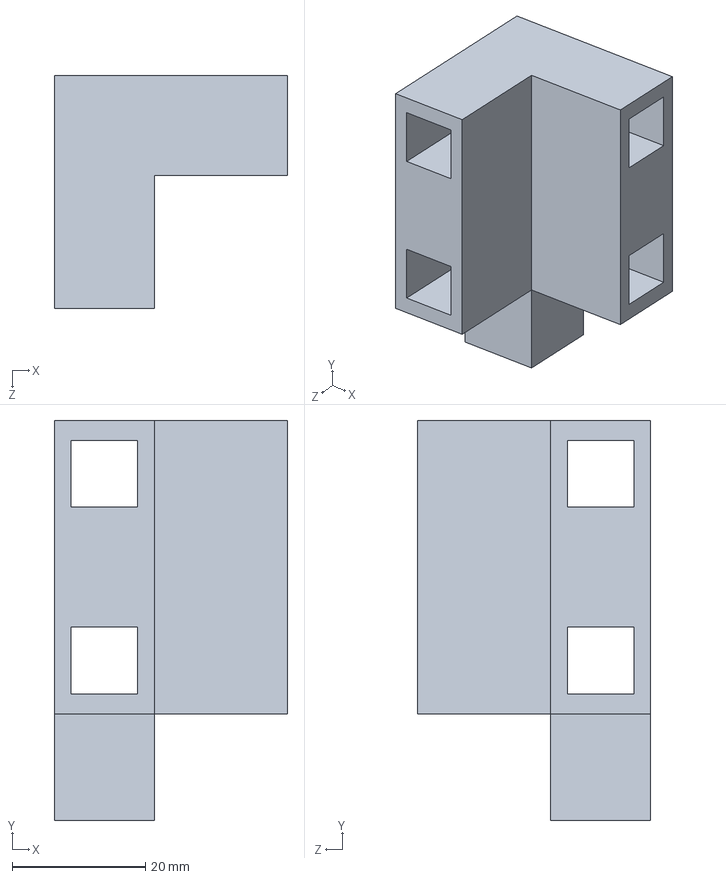
[picture p114: CAD file, 2026-05-20]
oodk(CAD model)/odk4（Generation 4）/444.SLDPRT
35.0 x 60.0 x 35.0 mm
