SauceSpoon/RBE206TC-submission/oodk(CAD model)/odk2（Generation 2）/print/架2.STEP

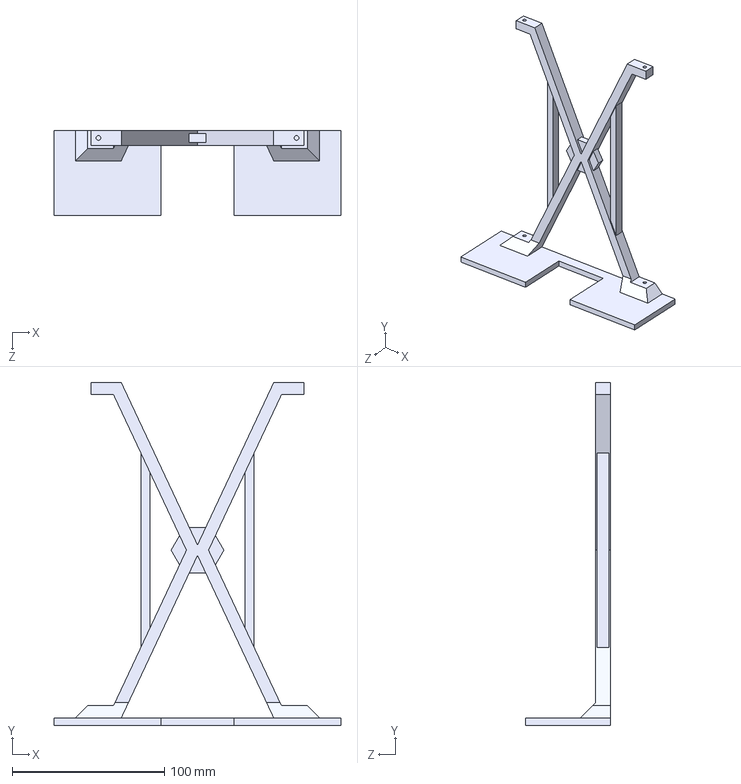
[picture p115: CAD file, 2026-05-20]
oodk(CAD model)/odk2（Generation 2）/print/架2.STEP
188.0 x 225.0 x 56.0 mm
