SauceSpoon/RBE206TC-submission/oodk(CAD model)/odk2（Generation 2）/大腿-右.SLDPRT

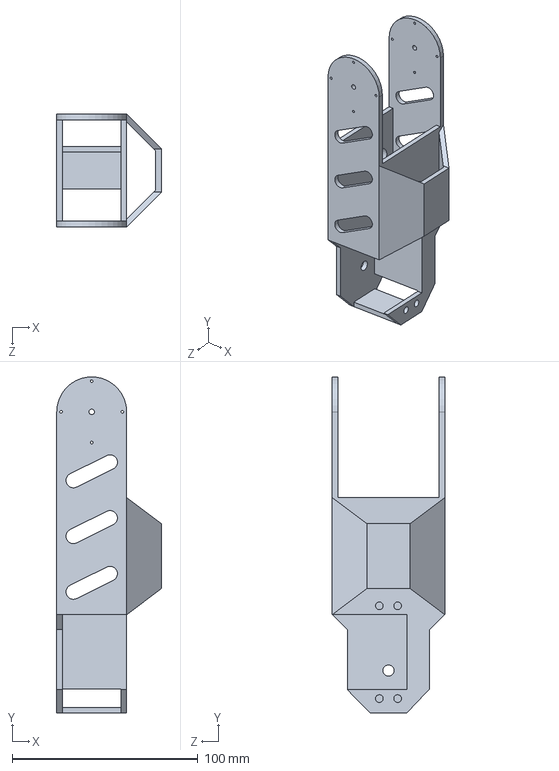
[picture p116: CAD file, 2026-05-20]
oodk(CAD model)/odk2（Generation 2）/大腿-右.SLDPRT
56.3 x 180.8 x 60.6 mm
