SauceSpoon/RBE206TC-submission/oodk(CAD model)/odk3（Generation 3）/print/11.STEP

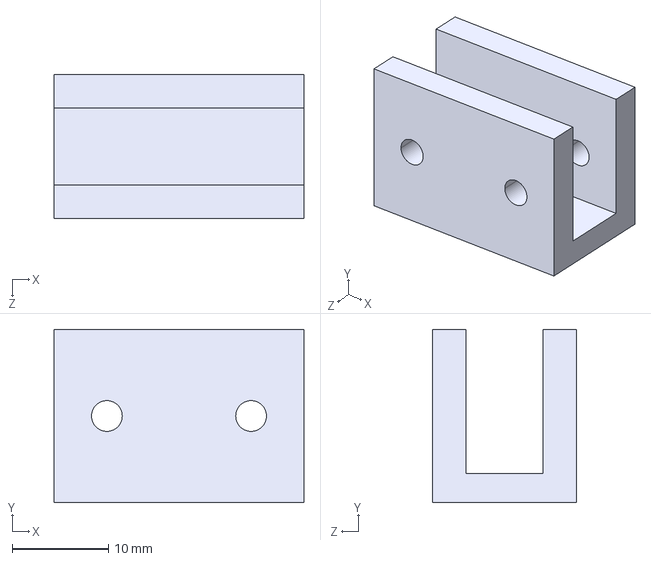
[picture p117: CAD file, 2026-05-20]
oodk(CAD model)/odk3（Generation 3）/print/11.STEP
26.0 x 18.0 x 15.0 mm
