SauceSpoon/RBE206TC-submission/oodk(CAD model)/odk3（Generation 3）/Sensor Ultrasonic.SLDPRT

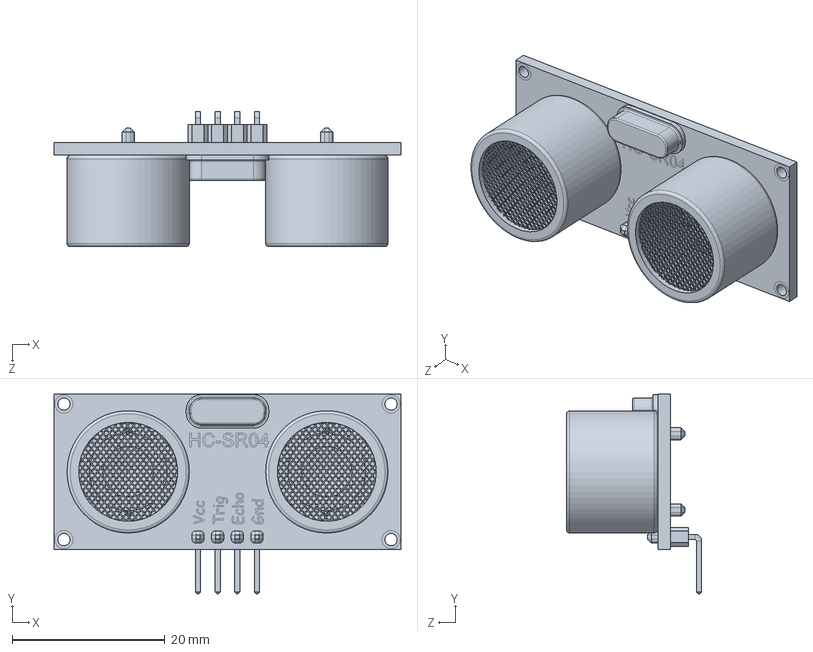
[picture p118: CAD file, 2026-05-20]
oodk(CAD model)/odk3（Generation 3）/Sensor Ultrasonic.SLDPRT
45.4 x 26.1 x 17.7 mm
