SauceSpoon/RBE206TC-submission/oodk(CAD model)/odk4（Generation 4）/print/c_pl_.STEP

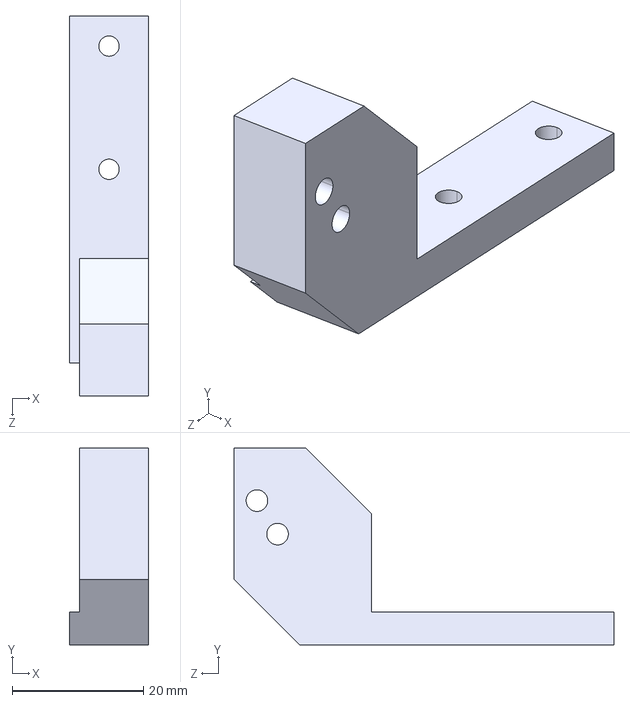
[picture p119: CAD file, 2026-05-20]
oodk(CAD model)/odk4（Generation 4）/print/c_pl_.STEP
12.0 x 30.0 x 58.0 mm
