SauceSpoon/RBE206TC-submission/oodk(CAD model)/odk3（Generation 3）/332.SLDPRT

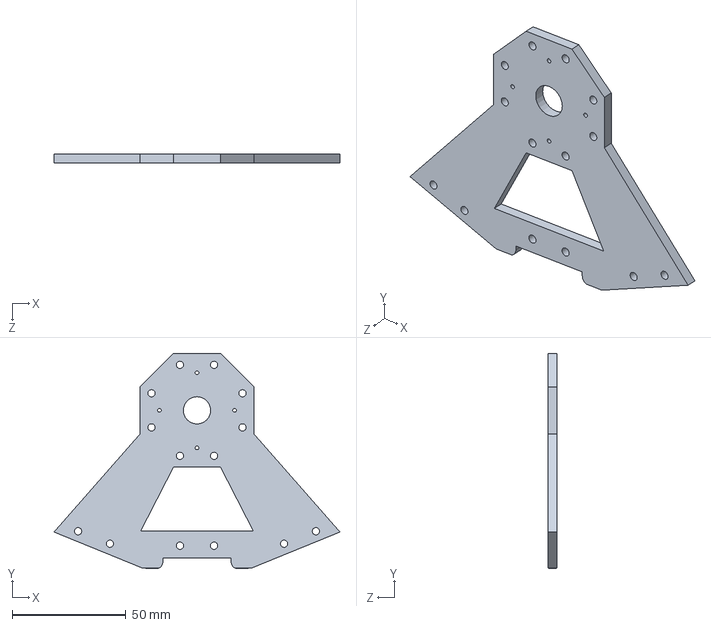
[picture p120: CAD file, 2026-05-20]
oodk(CAD model)/odk3（Generation 3）/332.SLDPRT
125.7 x 94.5 x 4.00 mm
