SauceSpoon/RBE206TC-submission/oodk(CAD model)/odk4（Generation 4）/cam_un.SLDPRT

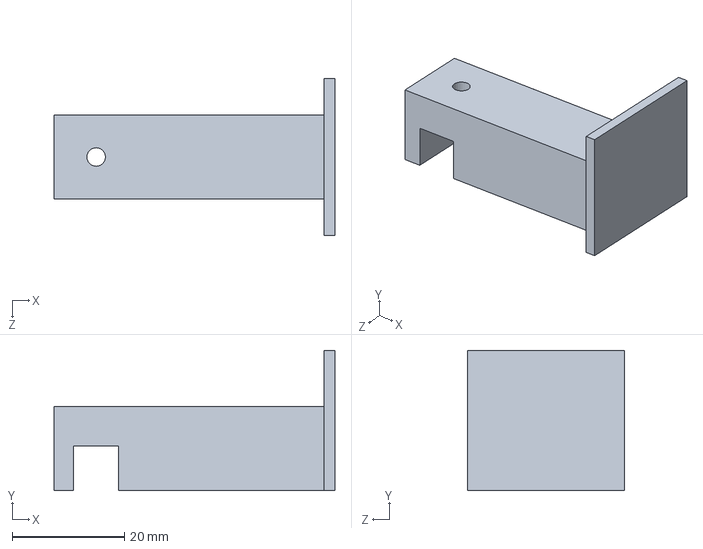
[picture p121: CAD file, 2026-05-20]
oodk(CAD model)/odk4（Generation 4）/cam_un.SLDPRT
50.0 x 25.0 x 28.0 mm
