SauceSpoon/RBE206TC-submission/oodk(CAD model)/odk4（Generation 4）/print/Mirrorfeet1.STEP

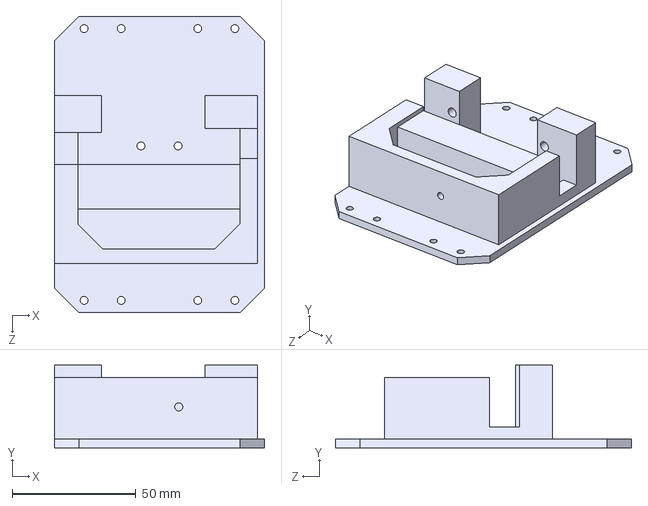
[picture p122: CAD file, 2026-05-20]
oodk(CAD model)/odk4（Generation 4）/print/Mirrorfeet1.STEP
85.0 x 33.5 x 120.0 mm
