SauceSpoon/RBE206TC-submission/oodk(CAD model)/odk2（Generation 2）/print/Mirrorthigh.STEP

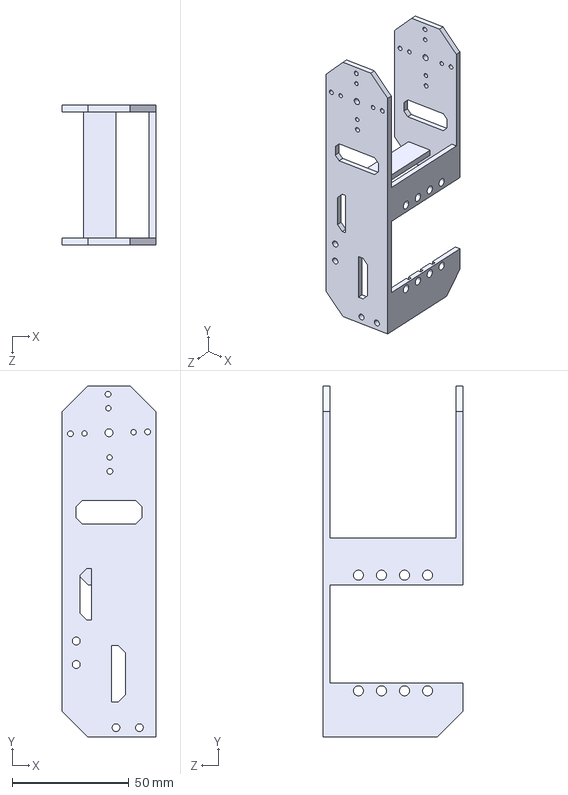
[picture p123: CAD file, 2026-05-20]
oodk(CAD model)/odk2（Generation 2）/print/Mirrorthigh.STEP
40.0 x 150.0 x 60.0 mm
