SauceSpoon/RBE206TC-submission/oodk(CAD model)/odk4（Generation 4）/print/344.STEP

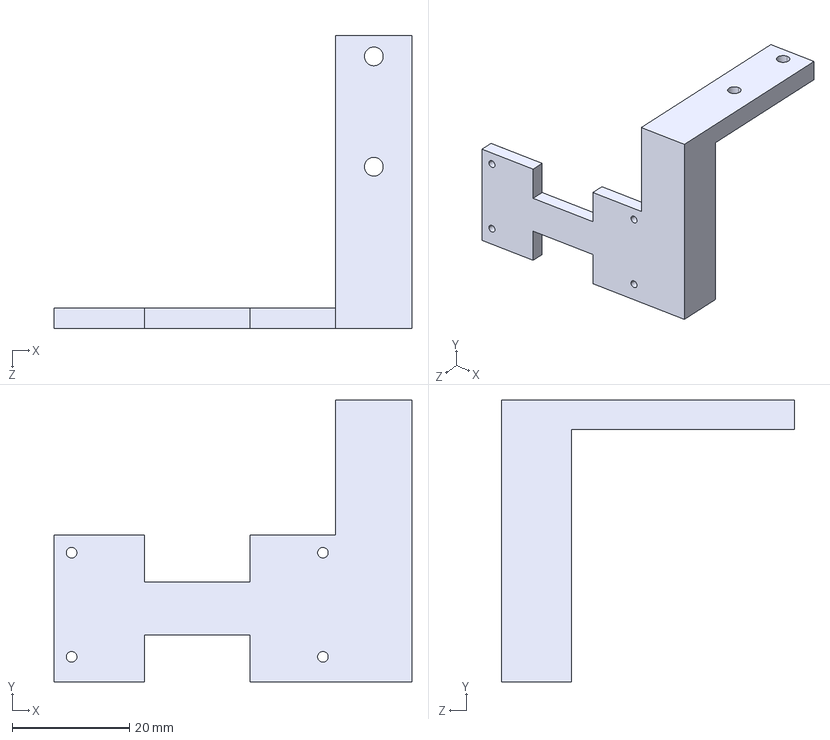
[picture p124: CAD file, 2026-05-20]
oodk(CAD model)/odk4（Generation 4）/print/344.STEP
61.0 x 48.0 x 50.0 mm
