SauceSpoon/RBE206TC-submission/oodk(CAD model)/odk2（Generation 2）/print/新plat.STEP

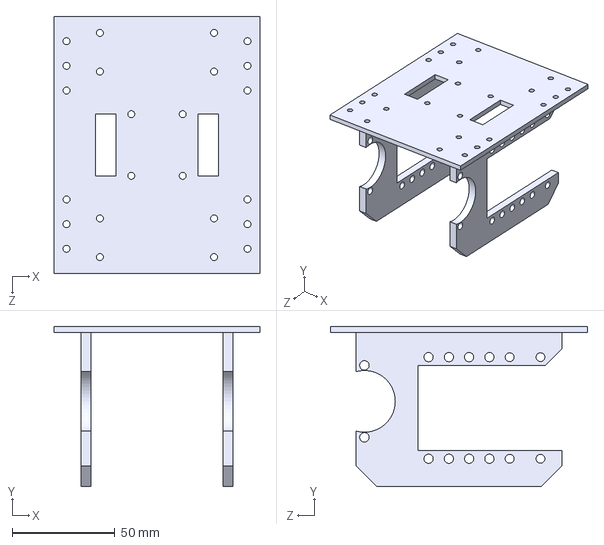
[picture p125: CAD file, 2026-05-20]
oodk(CAD model)/odk2（Generation 2）/print/新plat.STEP
100.0 x 78.0 x 125.0 mm
