SauceSpoon/RBE206TC-submission/oodk(CAD model)/odk2（Generation 2）/髋部.SLDPRT

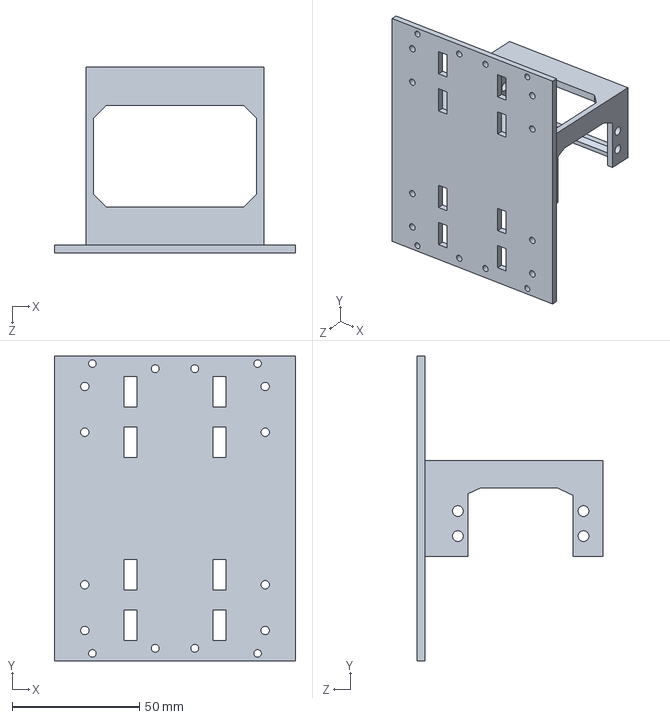
[picture p126: CAD file, 2026-05-20]
oodk(CAD model)/odk2（Generation 2）/髋部.SLDPRT
95.0 x 120.0 x 73.0 mm
