SauceSpoon/RBE206TC-submission/oodk(CAD model)/odk3（Generation 3）/print/3322.3mf

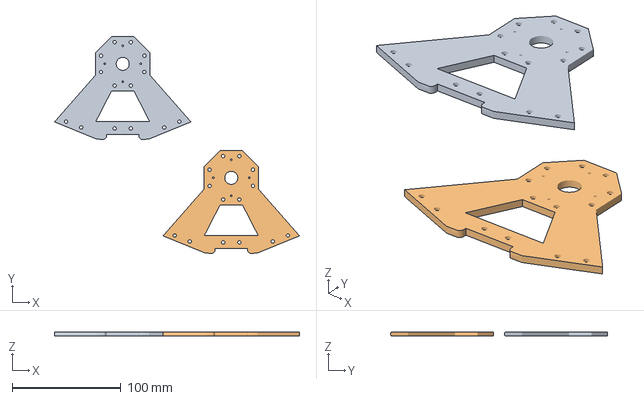
[picture p127: CAD file, 2026-05-20]
oodk(CAD model)/odk3（Generation 3）/print/3322.3mf
225.7 x 199.5 x 4.00 mm
332.STEP x 2
