SauceSpoon/RBE206TC-submission/oodk(CAD model)/odk3（Generation 3）/小腿.SLDPRT

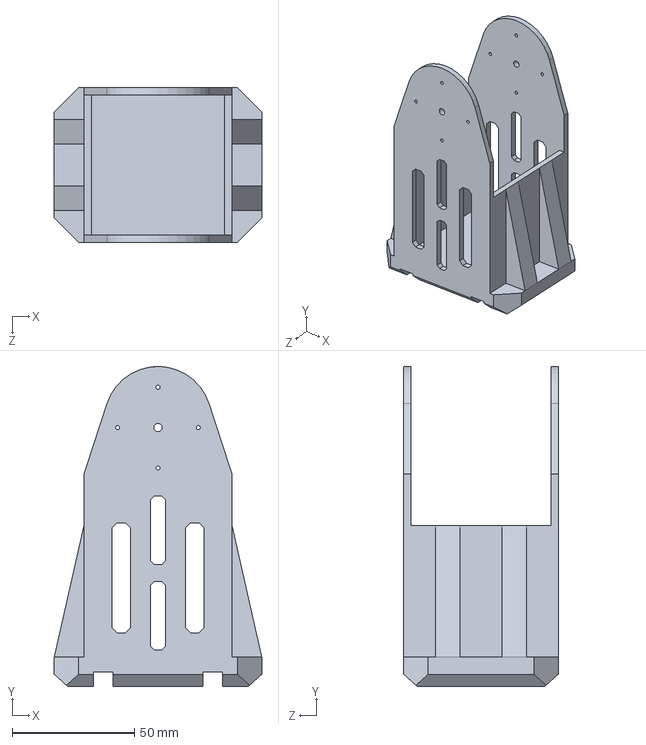
[picture p128: CAD file, 2026-05-20]
oodk(CAD model)/odk3（Generation 3）/小腿.SLDPRT
85.0 x 131.0 x 63.3 mm
