SauceSpoon/RBE206TC-submission/oodk(CAD model)/odk2（Generation 2）/MG90s.SLDPRT

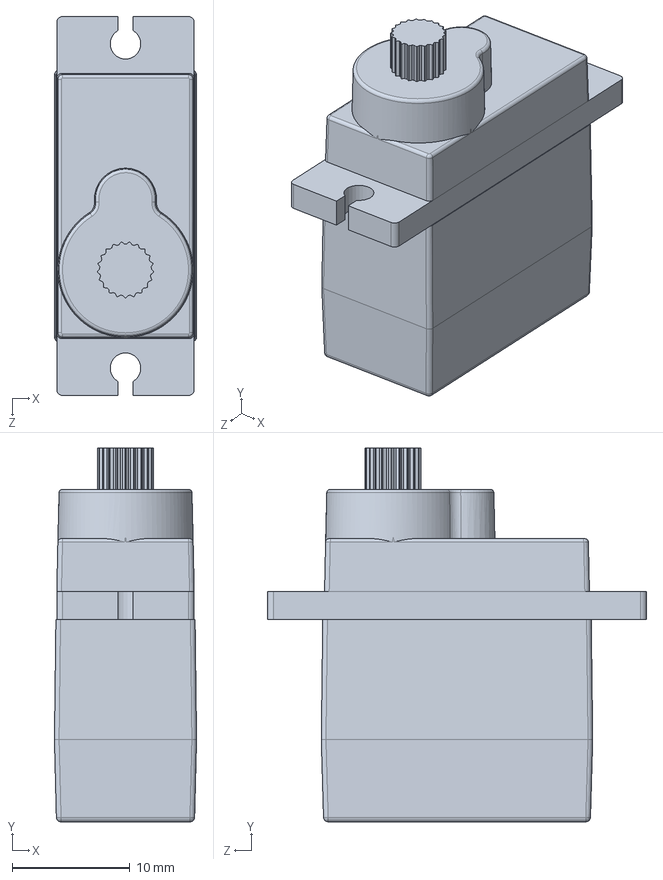
[picture p129: CAD file, 2026-05-20]
oodk(CAD model)/odk2（Generation 2）/MG90s.SLDPRT
12.1 x 31.8 x 32.2 mm
