SauceSpoon/RBE206TC-submission/oodk(CAD model)/odk4（Generation 4）/ESP32-S.SLDPRT

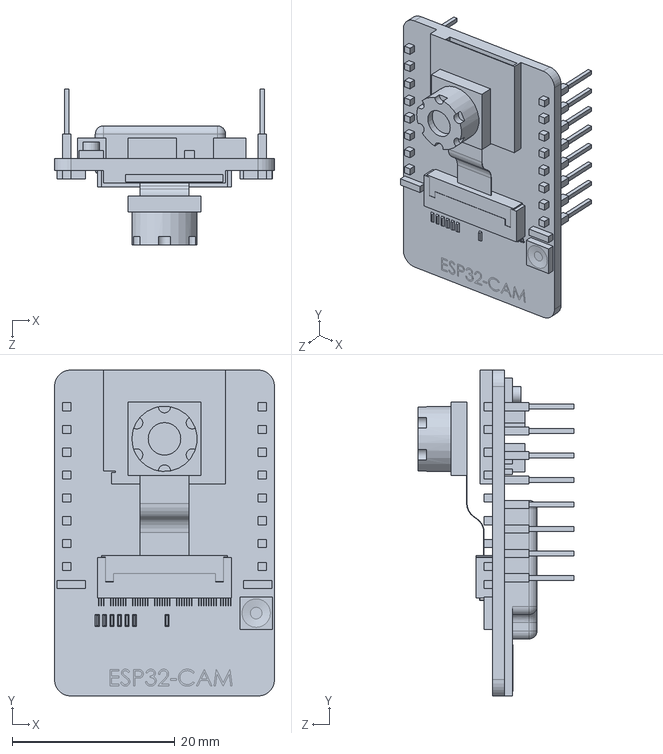
[picture p130: CAD file, 2026-05-20]
oodk(CAD model)/odk4（Generation 4）/ESP32-S.SLDPRT
27.0 x 40.0 x 19.1 mm
