SauceSpoon/RBE206TC-submission/oodk(CAD model)/odk4（Generation 4）/print/mor_.STEP

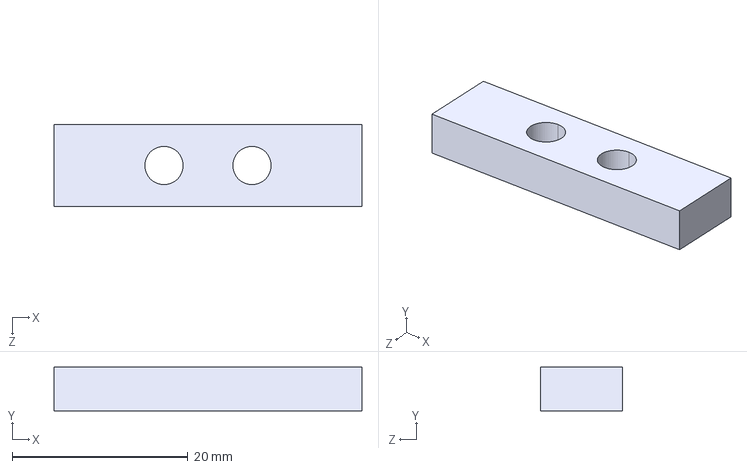
[picture p131: CAD file, 2026-05-20]
oodk(CAD model)/odk4（Generation 4）/print/mor_.STEP
35.0 x 5.00 x 9.30 mm
