SauceSpoon/RBE206TC-submission/oodk(CAD model)/odk4（Generation 4）/c.SLDPRT

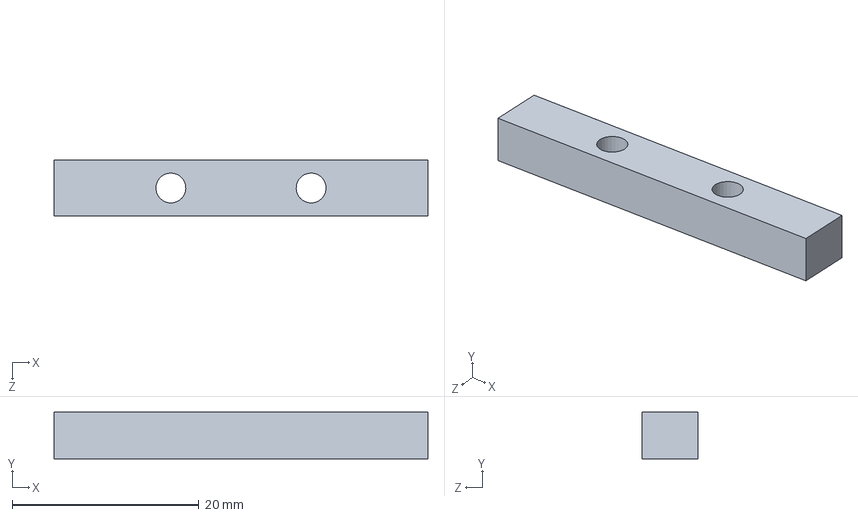
[picture p132: CAD file, 2026-05-20]
oodk(CAD model)/odk4（Generation 4）/c.SLDPRT
40.0 x 5.00 x 6.00 mm
