SauceSpoon/RBE206TC-submission/oodk(CAD model)/odk4（Generation 4）/print/leg2.STEP

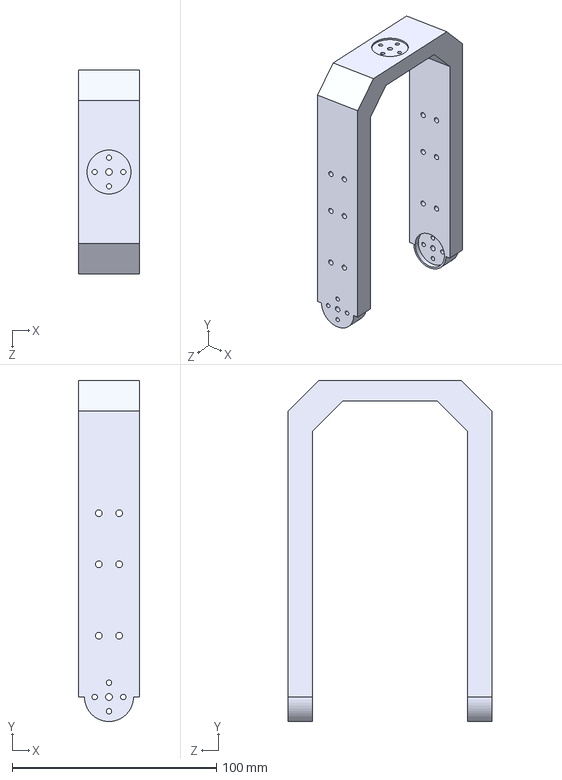
[picture p133: CAD file, 2026-05-20]
oodk(CAD model)/odk4（Generation 4）/print/leg2.STEP
30.0 x 167.0 x 100.0 mm
