SauceSpoon/RBE206TC-submission/oodk(CAD model)/odk4（Generation 4）/print/摄像机壳2.STEP

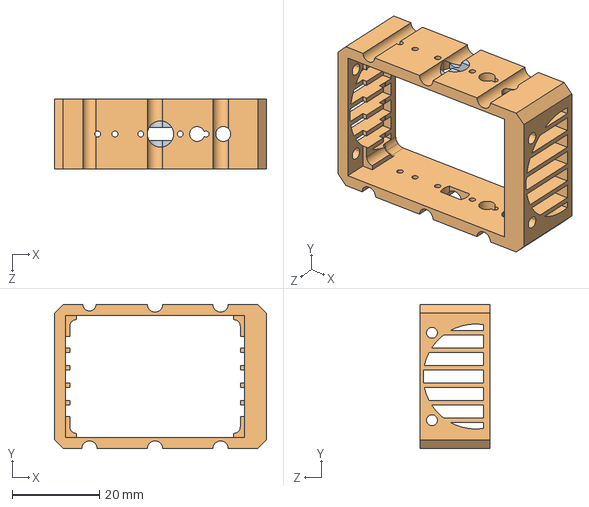
[picture p134: CAD file, 2026-05-20]
oodk(CAD model)/odk4（Generation 4）/print/摄像机壳2.STEP
48.5 x 33.0 x 16.0 mm
