SauceSpoon/RBE206TC-submission/oodk(CAD model)/odk2（Generation 2）/步进电机 28BYJ-48/Step Motor 28BYJ-48(1).JPG

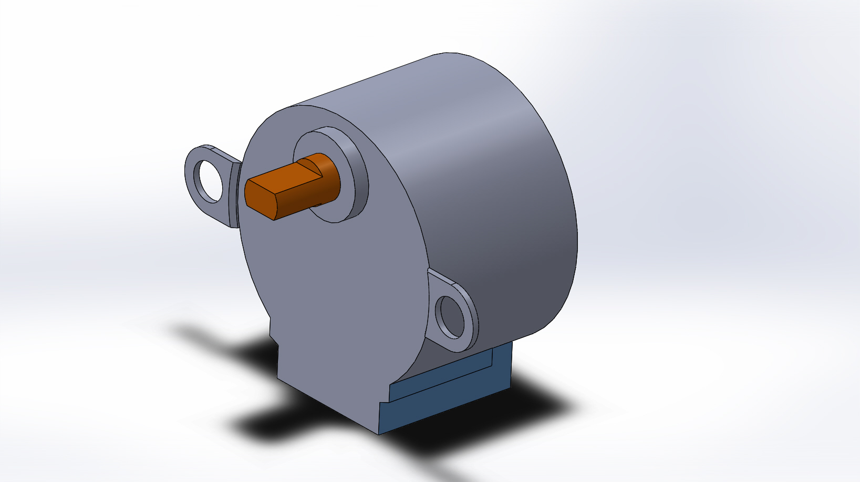
oodk(CAD model)/odk2（Generation 2）/步进电机 28BYJ-48/Step Motor 28BYJ-48(1).JPG
